salvatoreraccardi/OBJEX_LINK/boards/OBJEX_LINK-Rev1.7-C3_RISC-V/OBJEX Link v1.7-C3.jpg

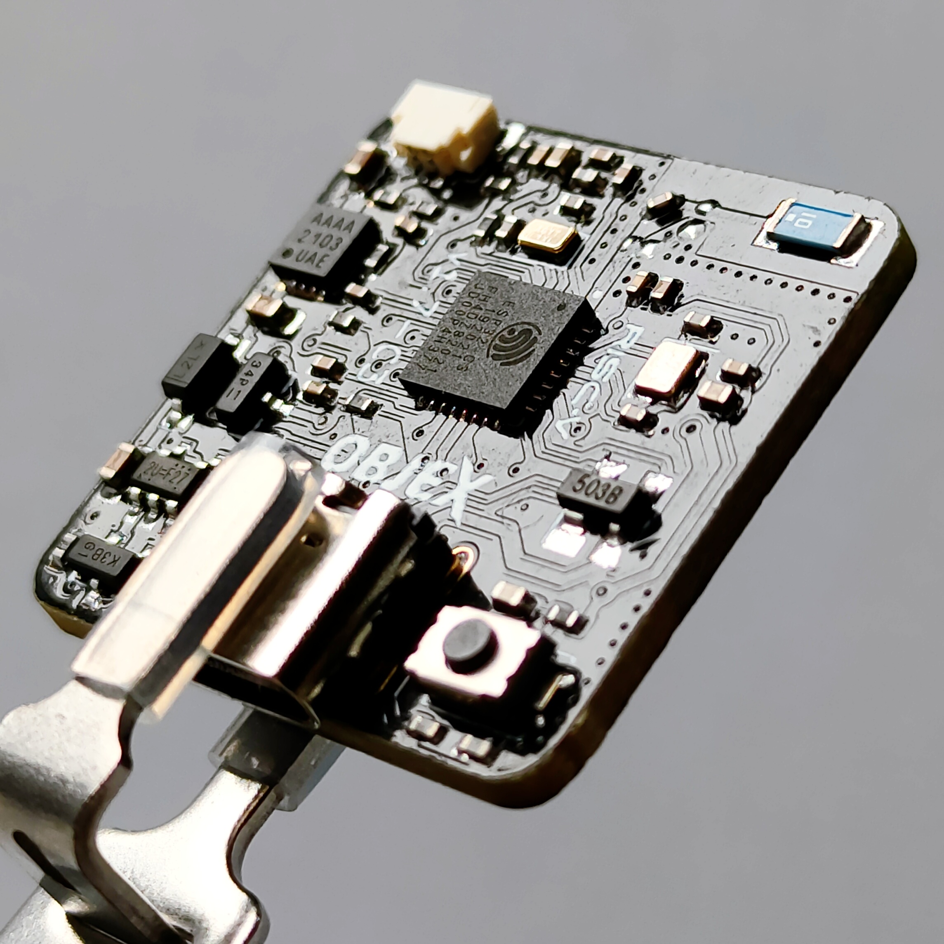
boards/OBJEX_LINK-Rev1.7-C3_RISC-V/OBJEX Link v1.7-C3.jpg
