salvatoreraccardi/OBJEX_LINK/dir/1-2.jpg

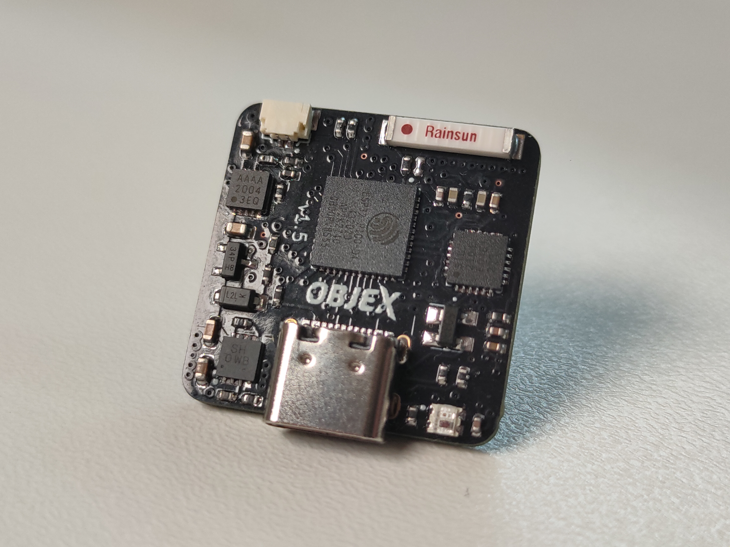
dir/1-2.jpg
