salvatoreraccardi/OBJEX_LINK/dir/1.jpg

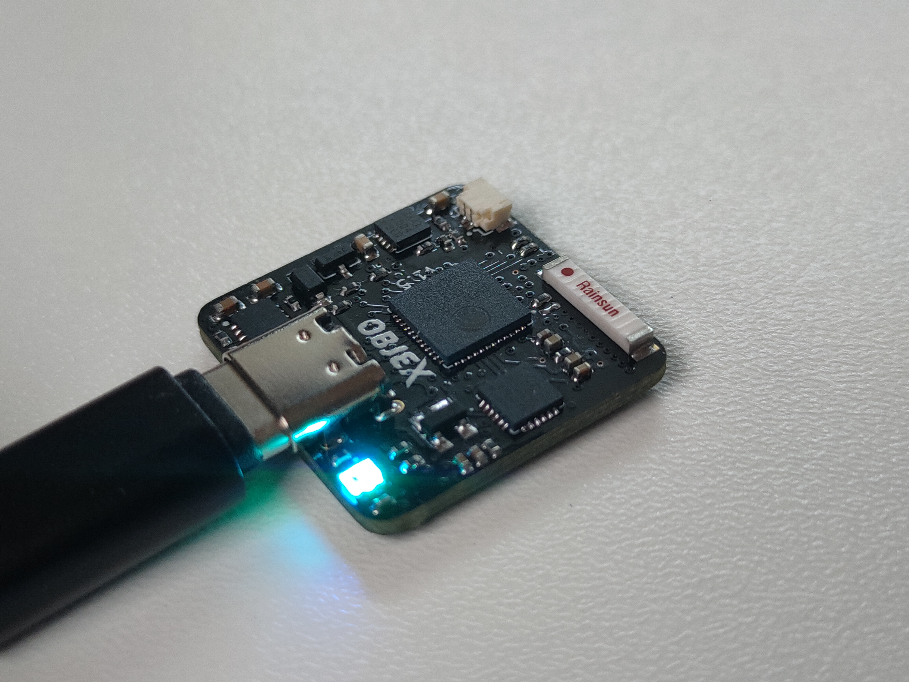
dir/1.jpg
