salvatoreraccardi/OBJEX_LINK/dir/2-1.png

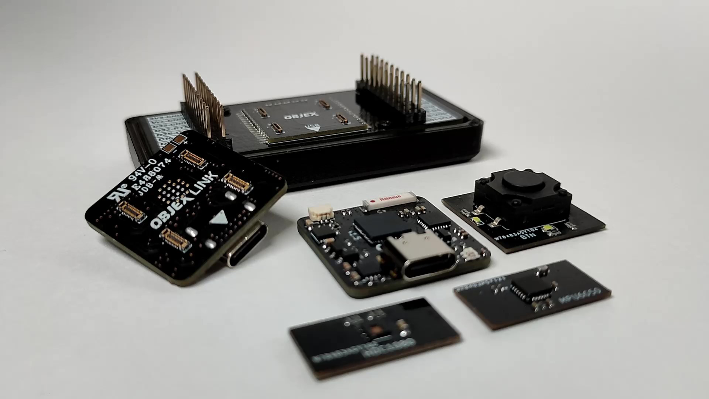
dir/2-1.png
