salvatoreraccardi/OBJEX_LINK/dir/2-3.jpg

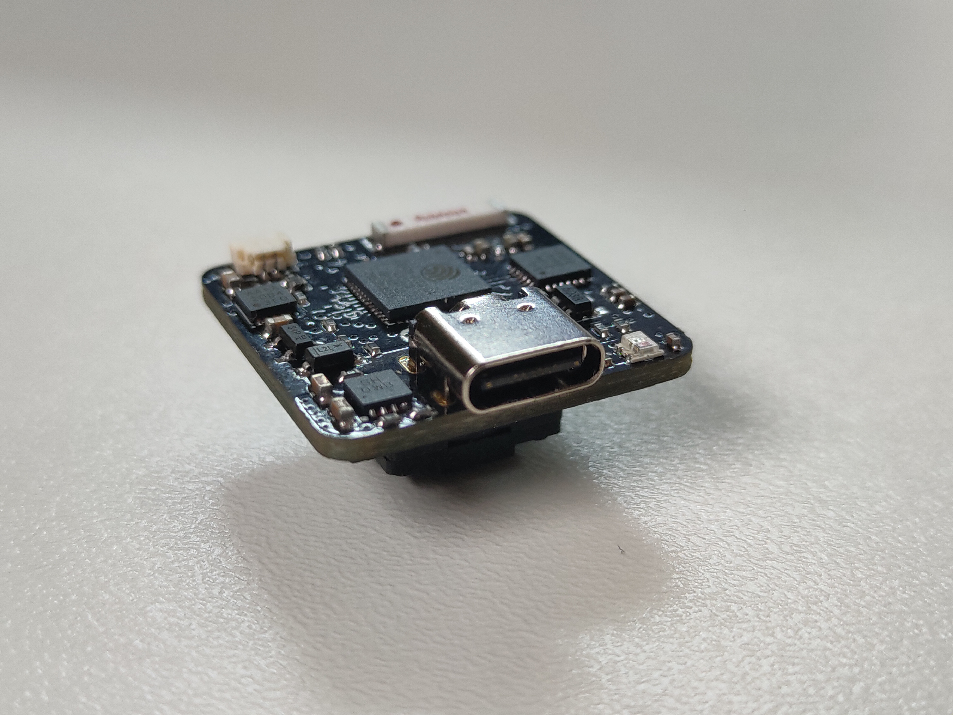
dir/2-3.jpg
