salvatoreraccardi/OBJEX_LINK/dir/2.jpg

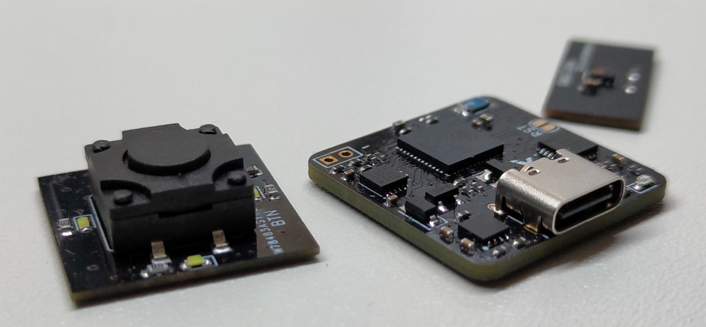
dir/2.jpg
