salvatoreraccardi/OBJEX_LINK/dir/3.jpg

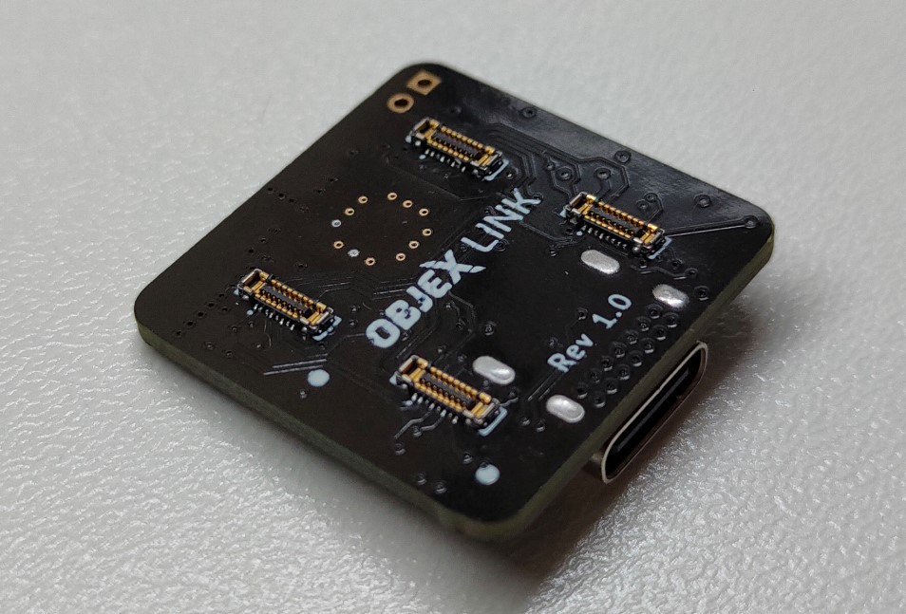
dir/3.jpg
