salvatoreraccardi/OBJEX_LINK/dir/3D_2.jpg

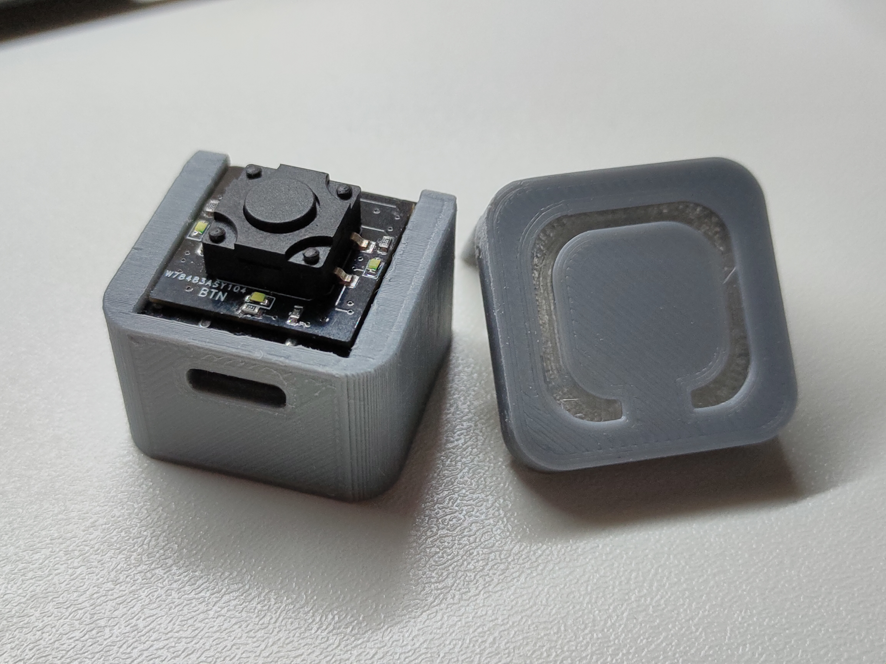
dir/3D_2.jpg
