salvatoreraccardi/OBJEX_LINK/dir/3D_3.jpg

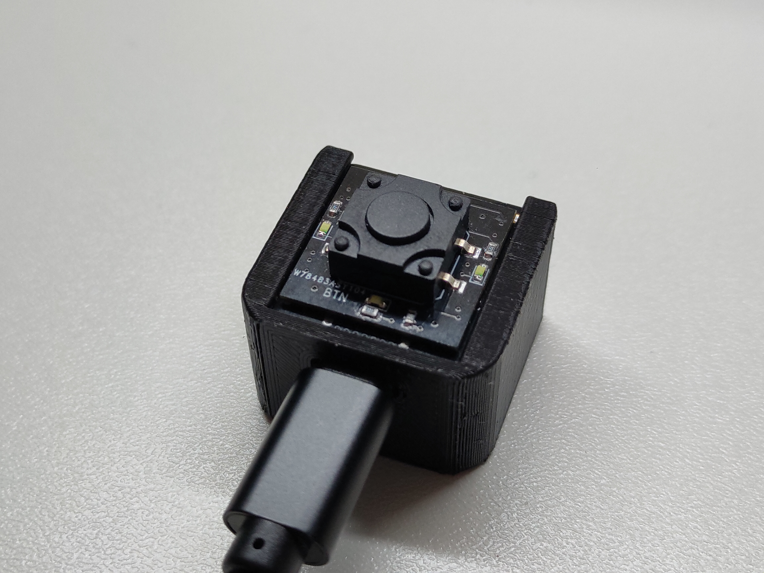
dir/3D_3.jpg
