salvatoreraccardi/OBJEX_LINK/dir/3D_4.jpg

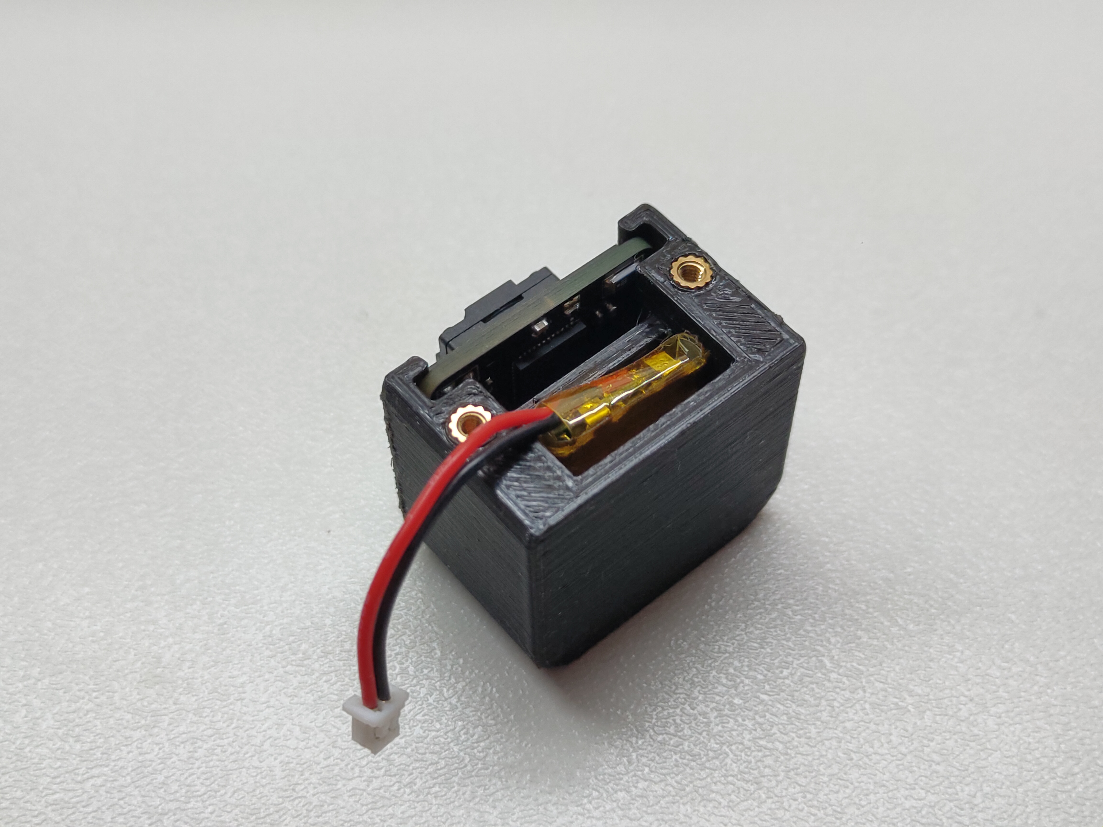
dir/3D_4.jpg
