salvatoreraccardi/OBJEX_LINK/dir/3D_5.jpg

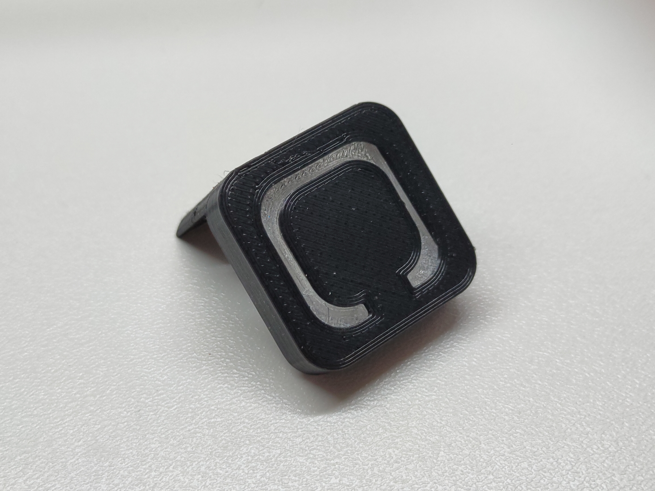
dir/3D_5.jpg
