salvatoreraccardi/OBJEX_LINK/dir/4.jpg

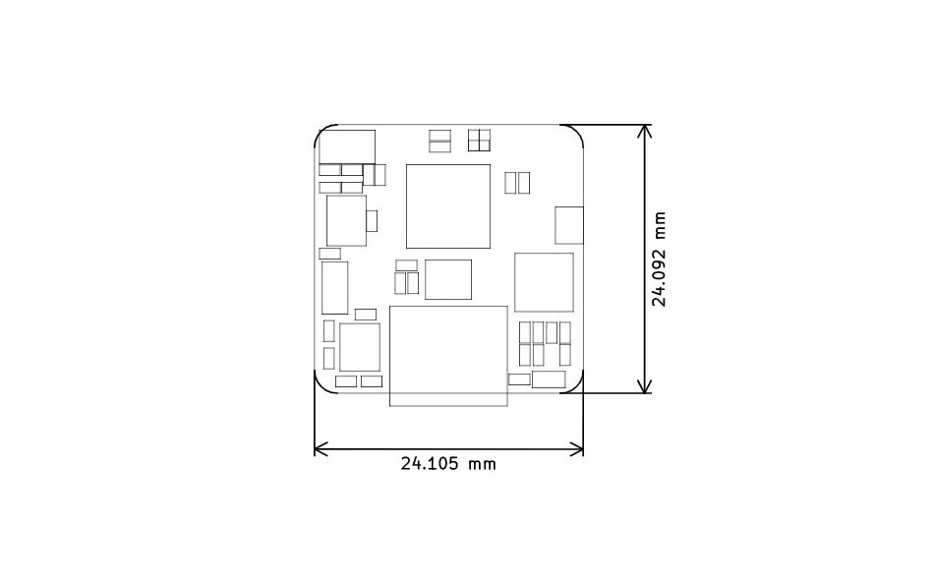
dir/4.jpg
