salvatoreraccardi/OBJEX_LINK/dir/5.jpg

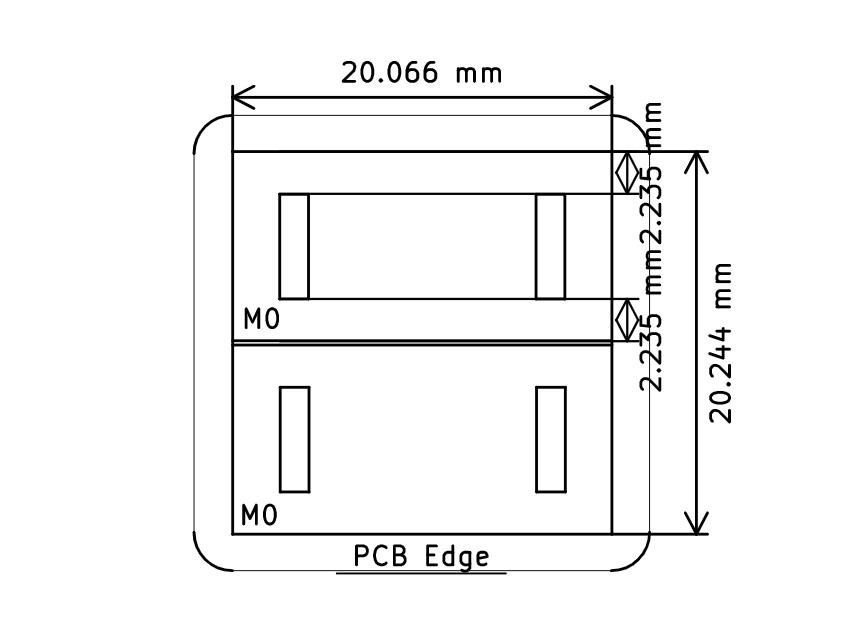
dir/5.jpg
