salvatoreraccardi/OBJEX_LINK/dir/blockdiagram/1.png

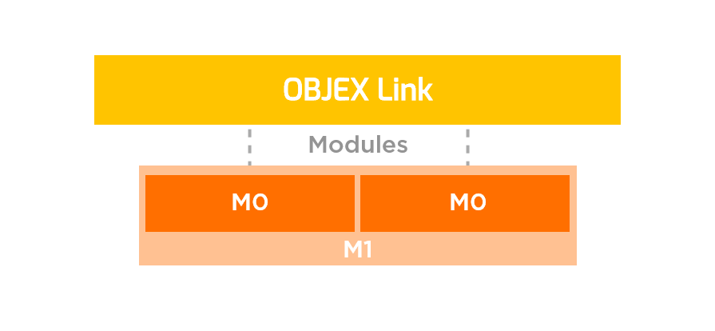
dir/blockdiagram/1.png
