salvatoreraccardi/OBJEX_LINK/dir/Blockdiagram_1.png

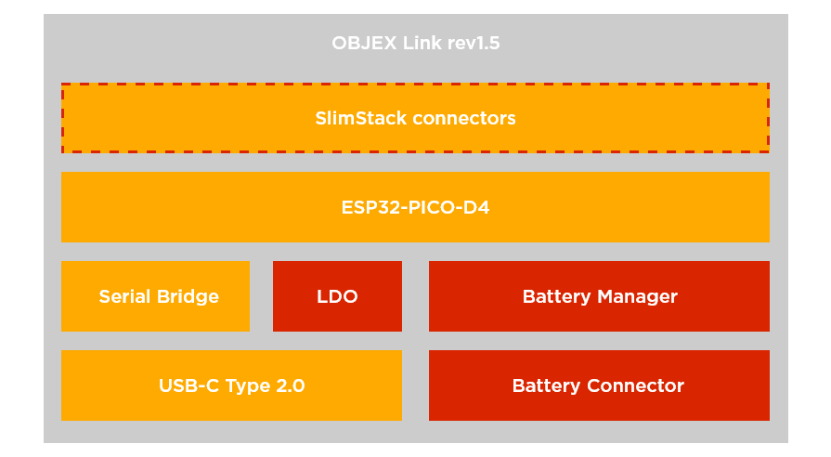
dir/Blockdiagram_1.png
