salvatoreraccardi/OBJEX_LINK/dir/Flex_1.png

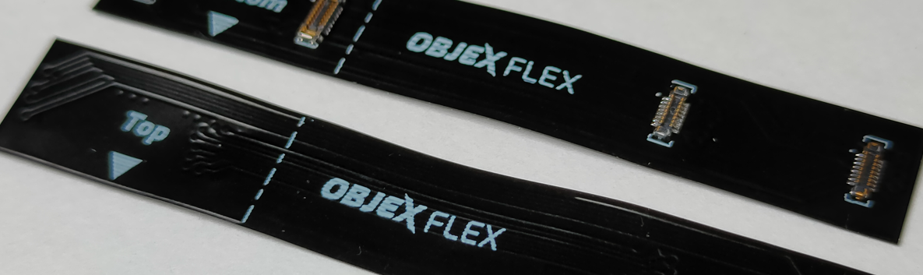
dir/Flex_1.png
