salvatoreraccardi/OBJEX_LINK/dir/Flex_2.png

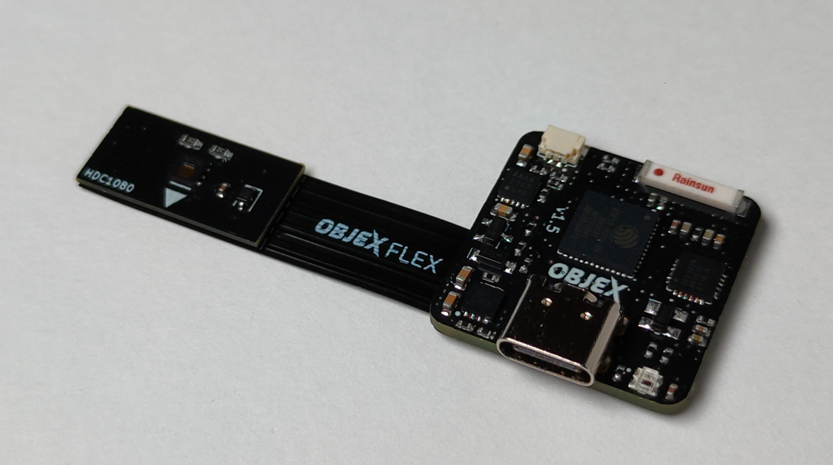
dir/Flex_2.png
