salvatoreraccardi/OBJEX_LINK/dir/Flex_3.png

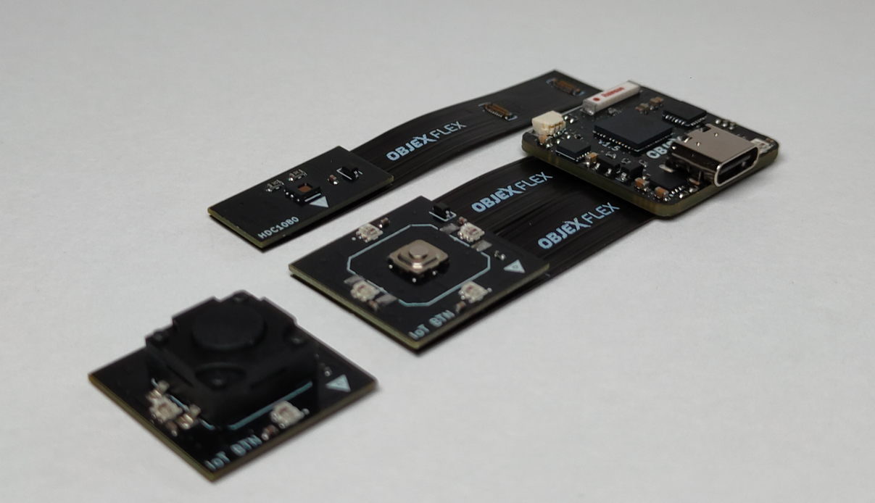
dir/Flex_3.png
