salvatoreraccardi/OBJEX_LINK/dir/Flex_4.png

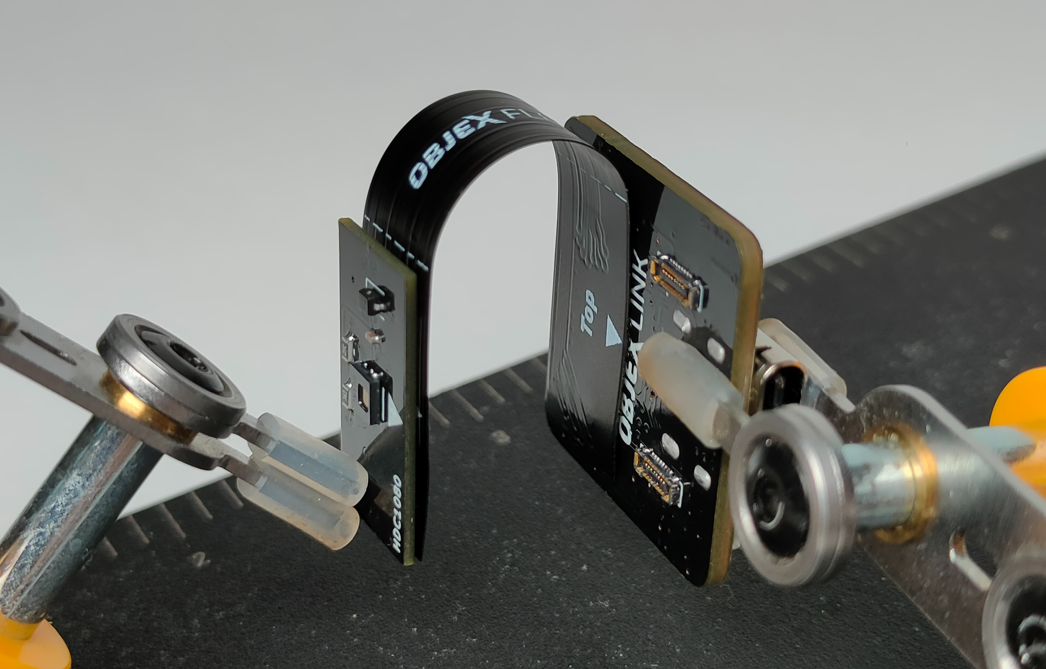
dir/Flex_4.png
