salvatoreraccardi/OBJEX_LINK/dir/Flex_5.png

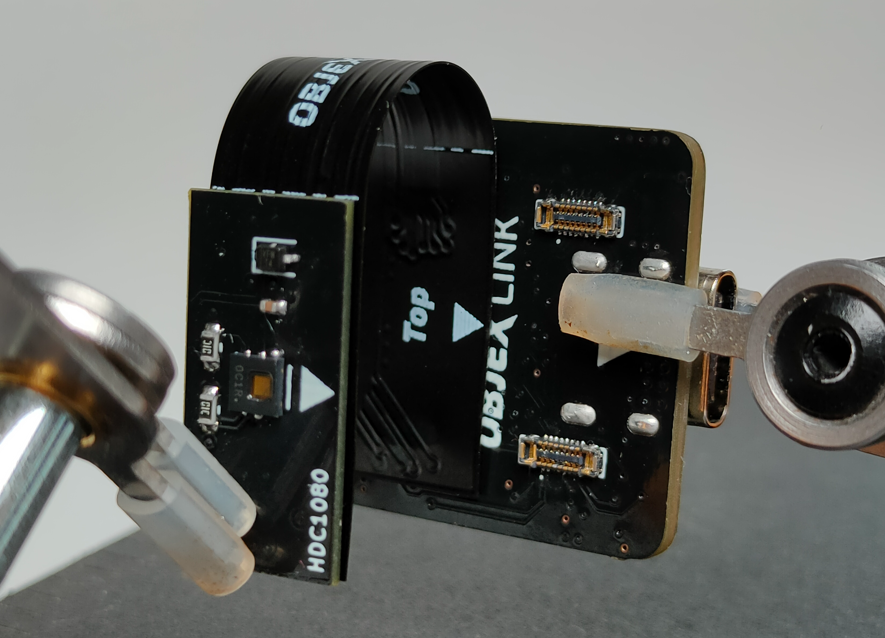
dir/Flex_5.png
