salvatoreraccardi/OBJEX_LINK/dir/Flex_7.jpg

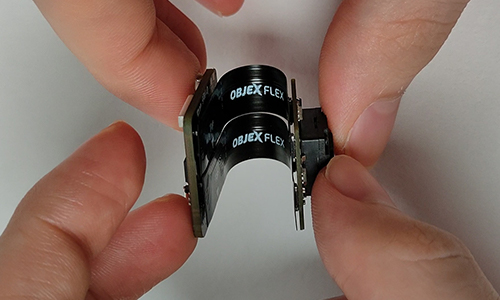
dir/Flex_7.jpg
