salvatoreraccardi/OBJEX_LINK/dir/graph-pwr_consumpition.png

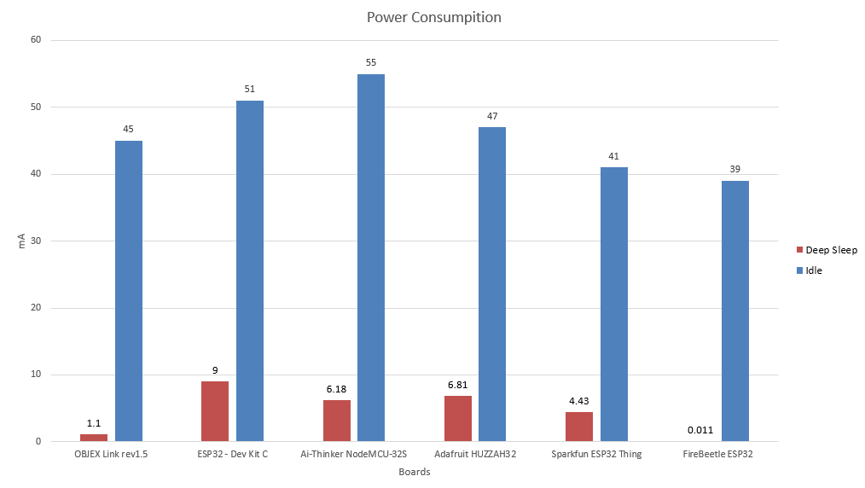
dir/graph-pwr_consumpition.png
