salvatoreraccardi/OBJEX_LINK/dir/IMG20210604104828.jpg

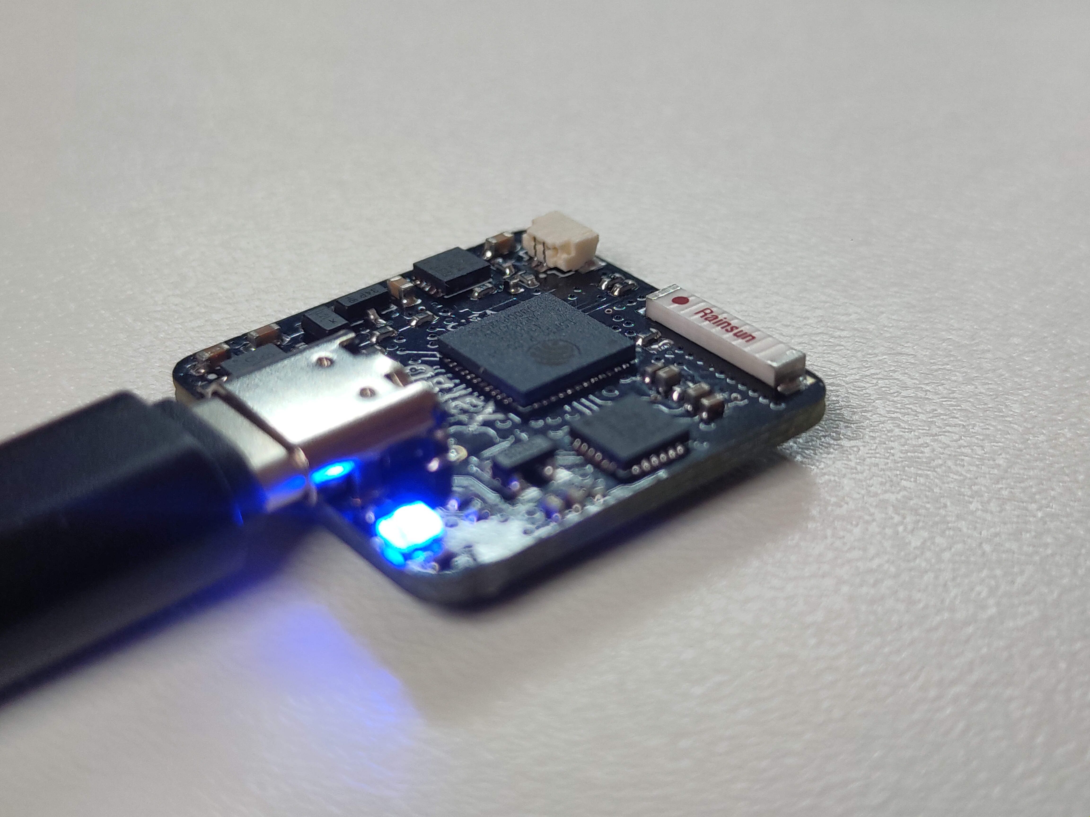
dir/IMG20210604104828.jpg
