salvatoreraccardi/OBJEX_LINK/dir/IMG20210604105308.jpg

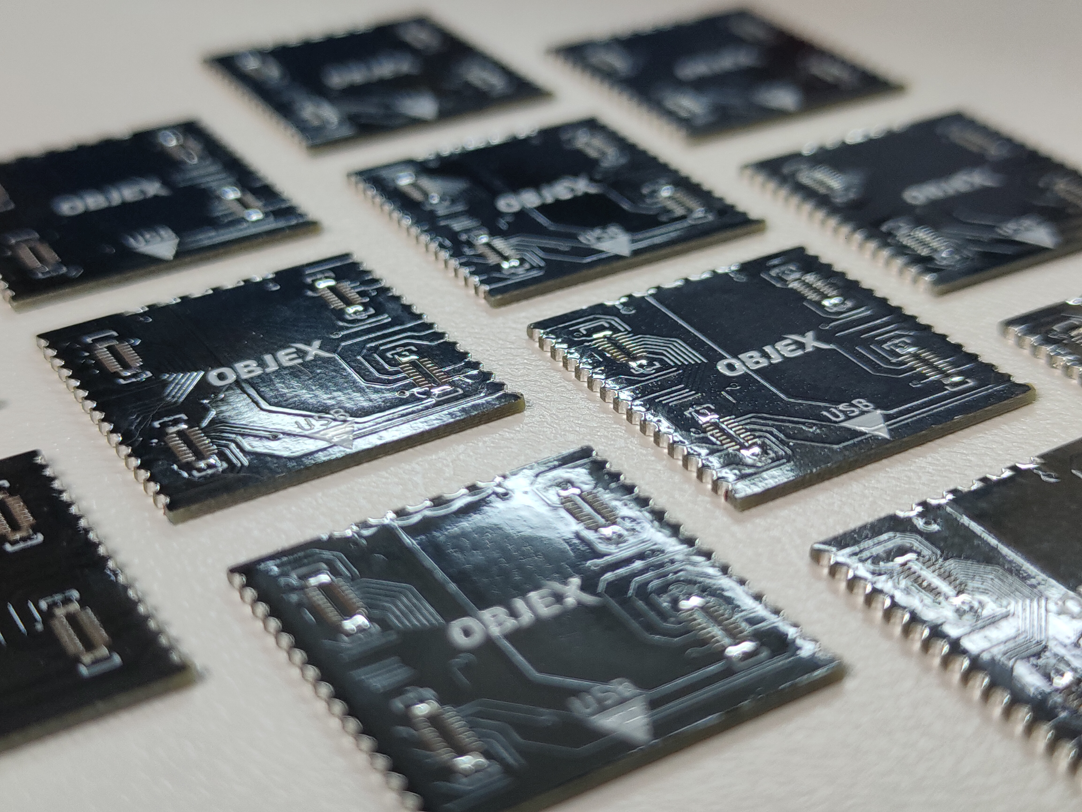
dir/IMG20210604105308.jpg
