salvatoreraccardi/OBJEX_LINK/dir/IMG20210604105436.jpg

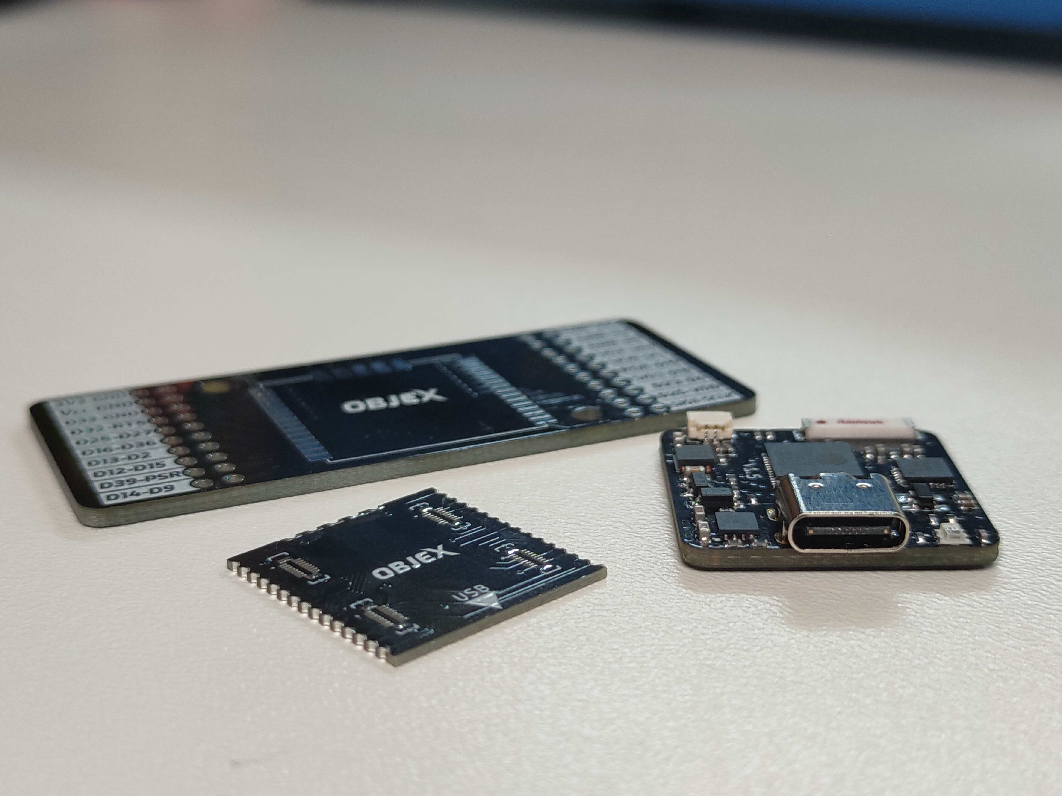
dir/IMG20210604105436.jpg
