salvatoreraccardi/OBJEX_LINK/dir/iotbuttonTypeA.png

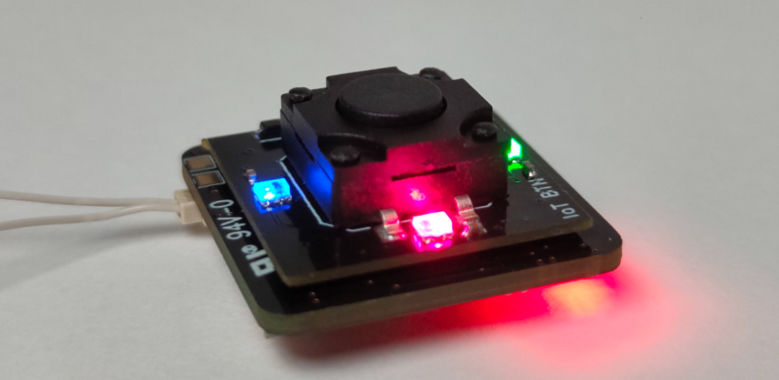
dir/iotbuttonTypeA.png
