salvatoreraccardi/OBJEX_LINK/dir/modules/HDC1080_1.5.png

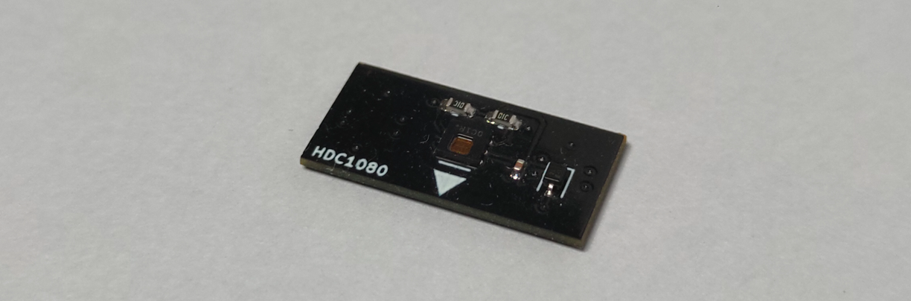
dir/modules/HDC1080_1.5.png
