salvatoreraccardi/OBJEX_LINK/dir/modules/IoT_btn_rgb-1.png

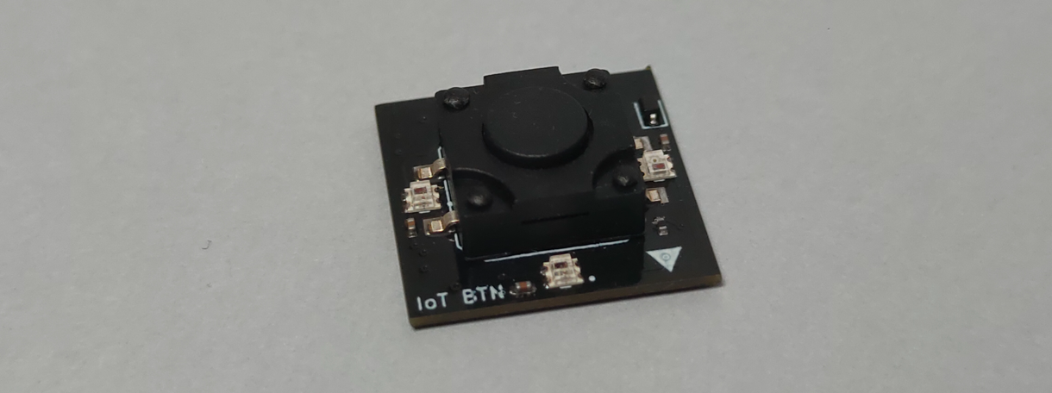
dir/modules/IoT_btn_rgb-1.png
