salvatoreraccardi/OBJEX_LINK/dir/modules/IoT_btn_rgb-2.png

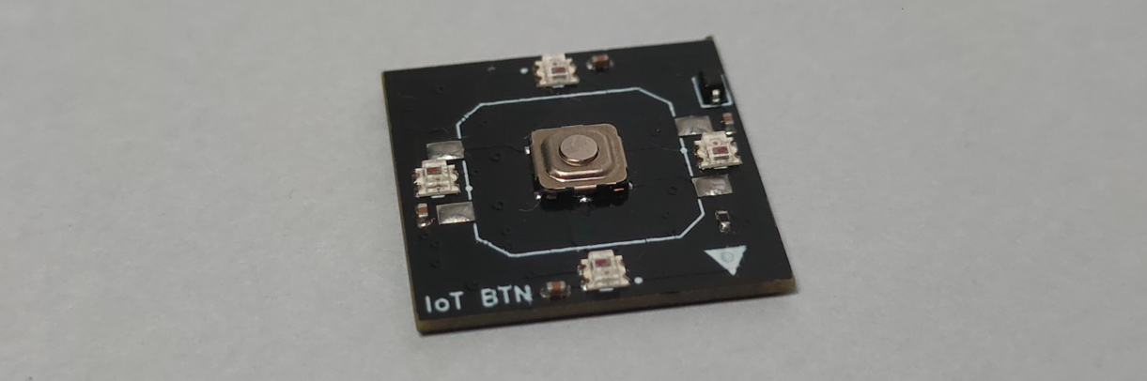
dir/modules/IoT_btn_rgb-2.png
