salvatoreraccardi/OBJEX_LINK/dir/modules/MPU6050_1.0.png

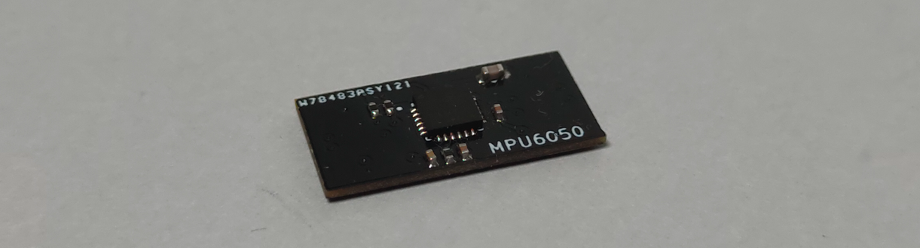
dir/modules/MPU6050_1.0.png
