salvatoreraccardi/OBJEX_LINK/dir/modules/ProtoBoard.png

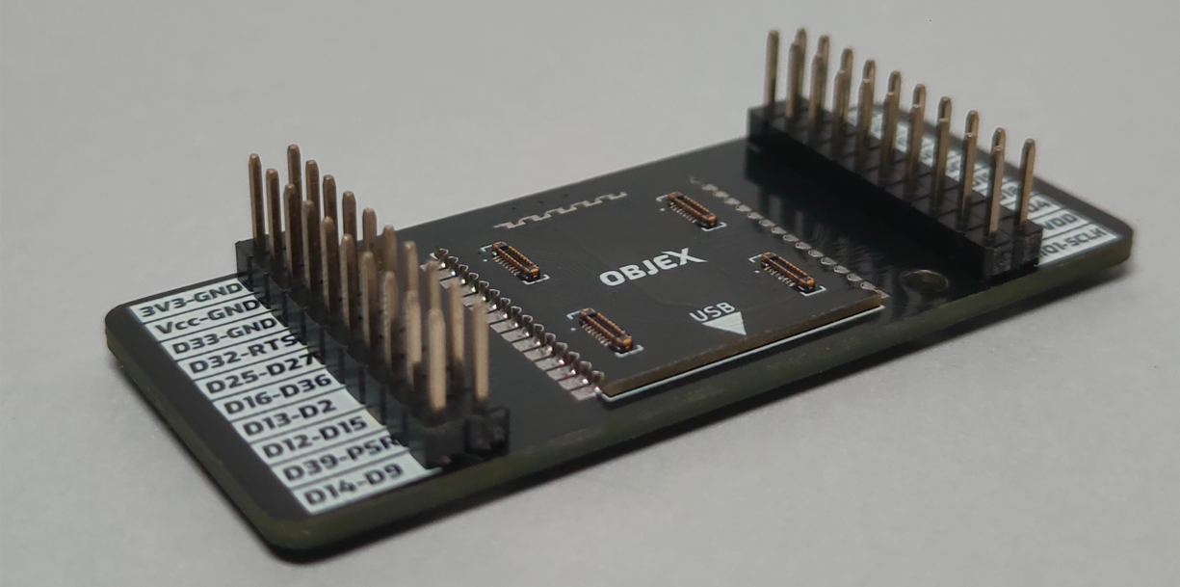
dir/modules/ProtoBoard.png
