salvatoreraccardi/OBJEX_LINK/dir/objexlink&modules.png

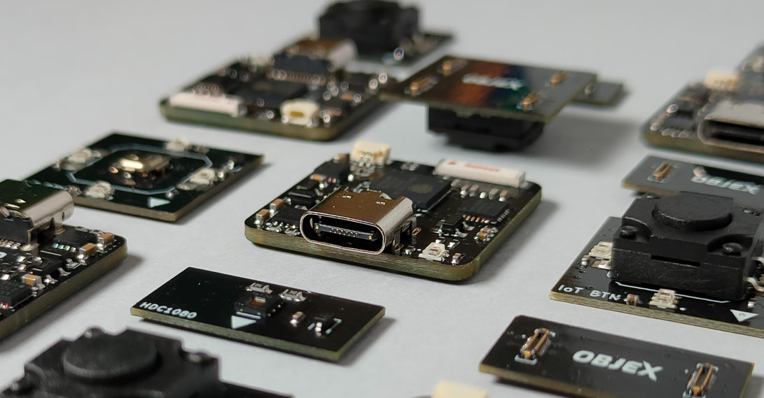
dir/objexlink&modules.png
