salvatoreraccardi/OBJEX_LINK/dir/Protoboard_1.png

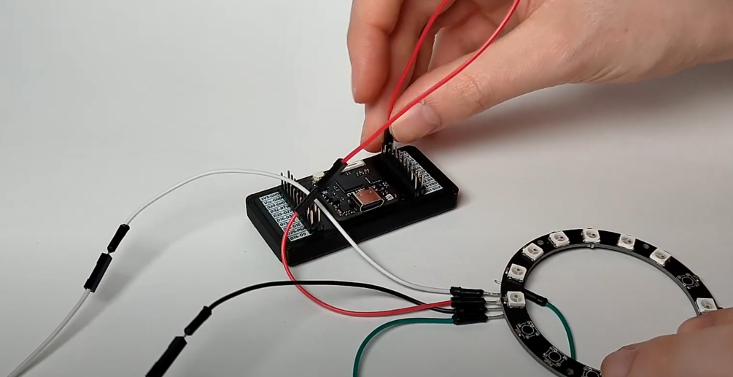
dir/Protoboard_1.png
