salvatoreraccardi/OBJEX_LINK/dir/QuickStart/1.png

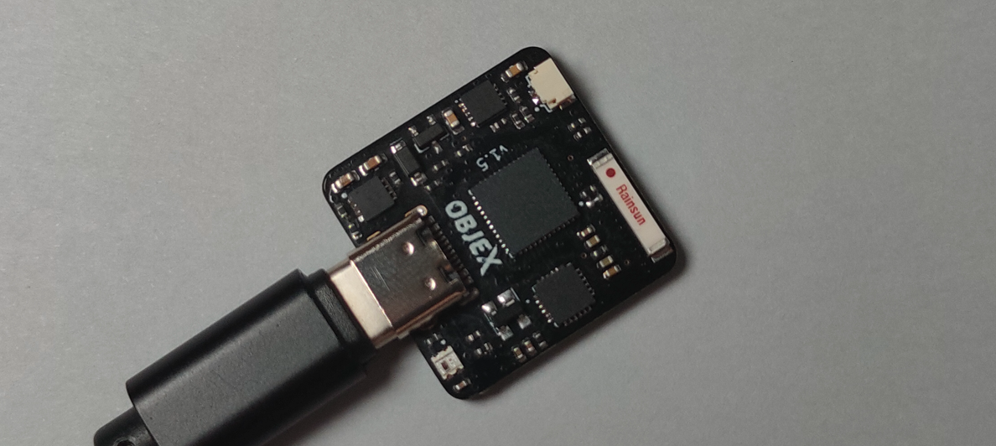
dir/QuickStart/1.png
