salvatoreraccardi/OBJEX_LINK/dir/QuickStart/2.png

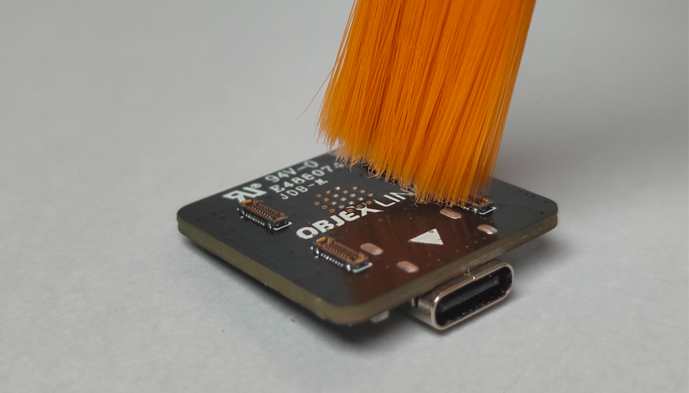
dir/QuickStart/2.png
