salvatoreraccardi/OBJEX_LINK/dir/QuickStart/3.png

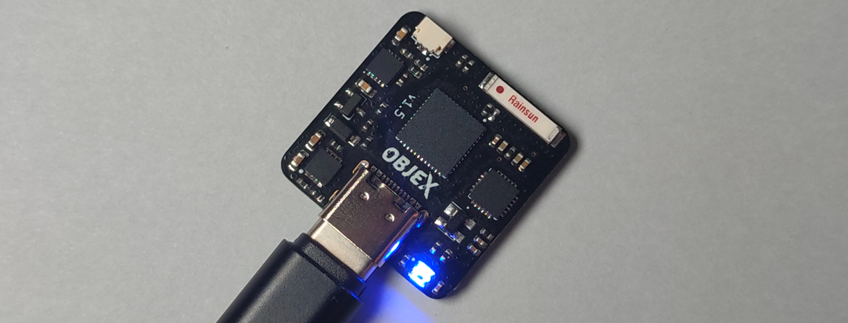
dir/QuickStart/3.png
