salvatoreraccardi/OBJEX_LINK/dir/QuickStart/4.png

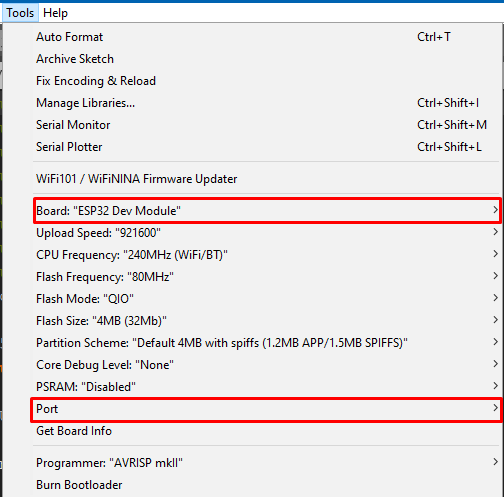
dir/QuickStart/4.png
