salvatoreraccardi/OBJEX_LINK/dir/QuickStart/5.png

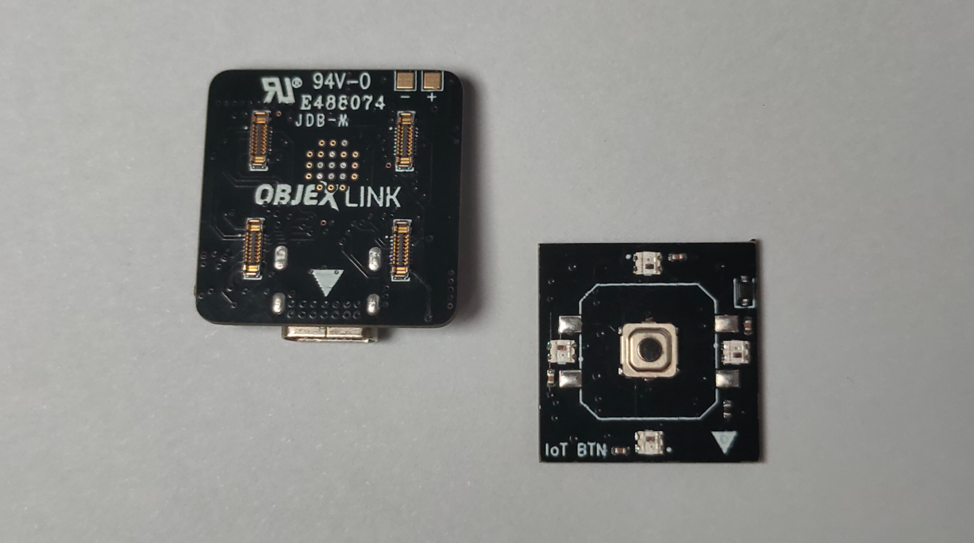
dir/QuickStart/5.png
