salvatoreraccardi/OBJEX_LINK/dir/QuickStart/6.png

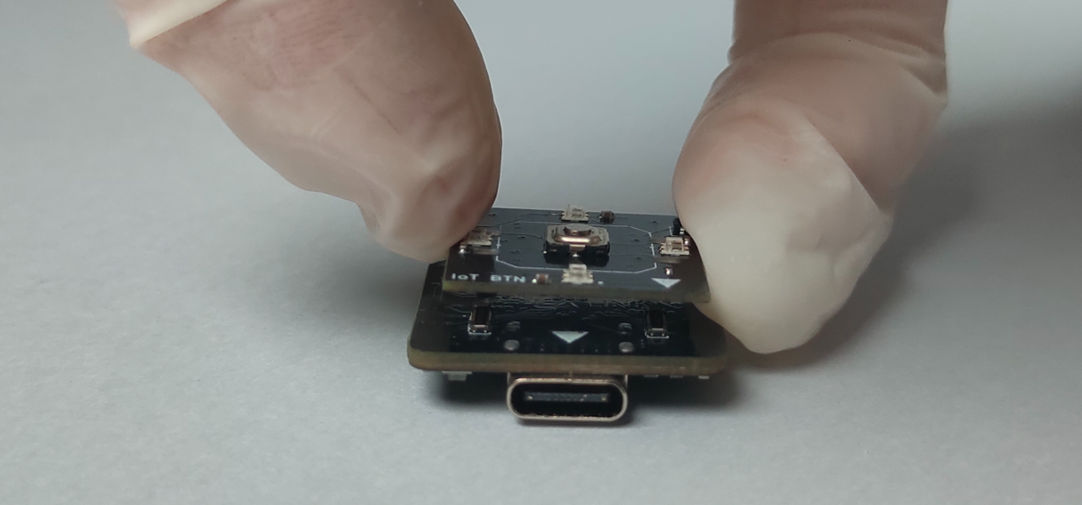
dir/QuickStart/6.png
