salvatoreraccardi/OBJEX_LINK/dir/QuickStart/7.png

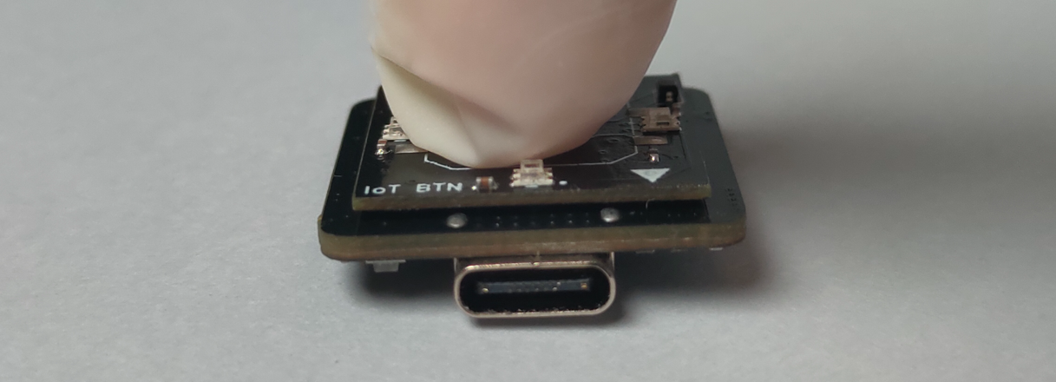
dir/QuickStart/7.png
