salvatoreraccardi/OBJEX_LINK/dir/QuickStart/8.png

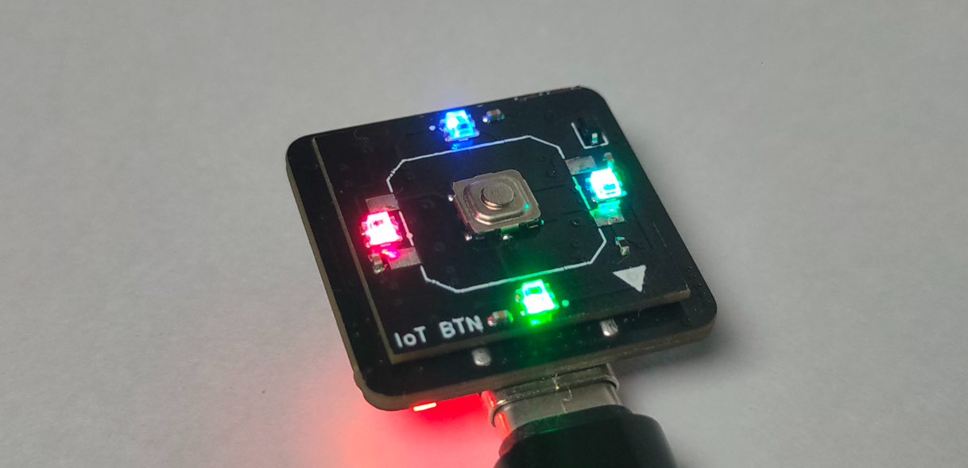
dir/QuickStart/8.png
