salvatoreraccardi/OBJEX_LINK/dir/QuickStart/9.png

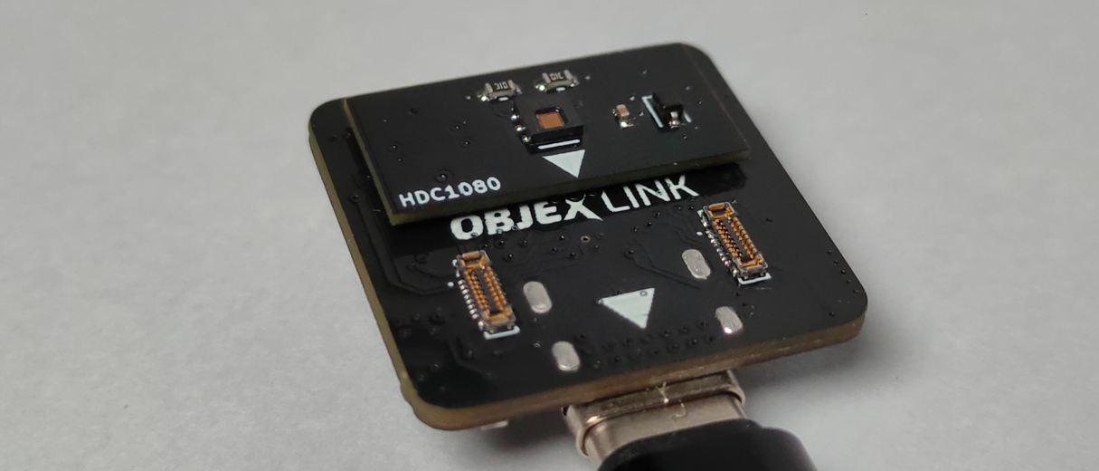
dir/QuickStart/9.png
