salvatoreraccardi/OBJEX_LINK/dir/QuickStart/10.png

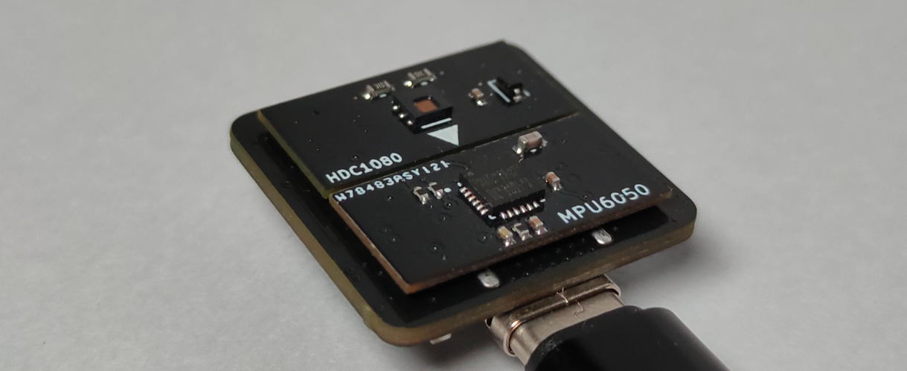
dir/QuickStart/10.png
