salvatoreraccardi/OBJEX_LINK/dir/QuickStart/12.png

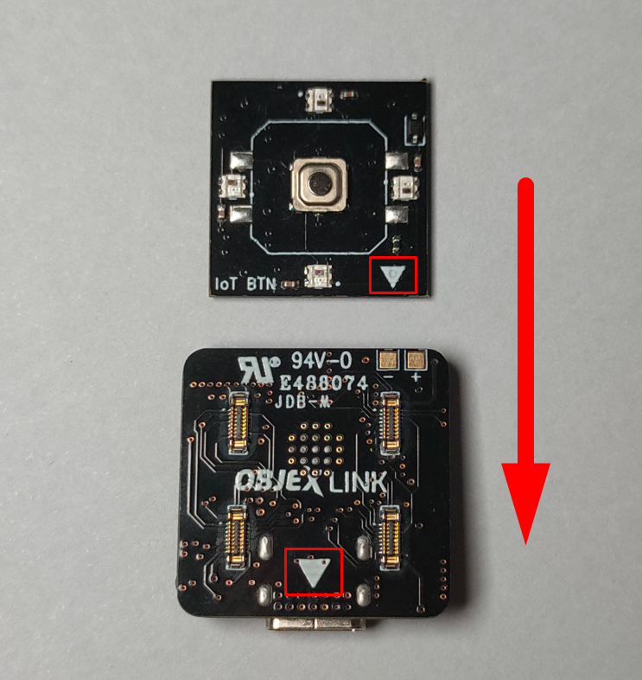
dir/QuickStart/12.png
