salvatoreraccardi/OBJEX_LINK/dir/rprog.png

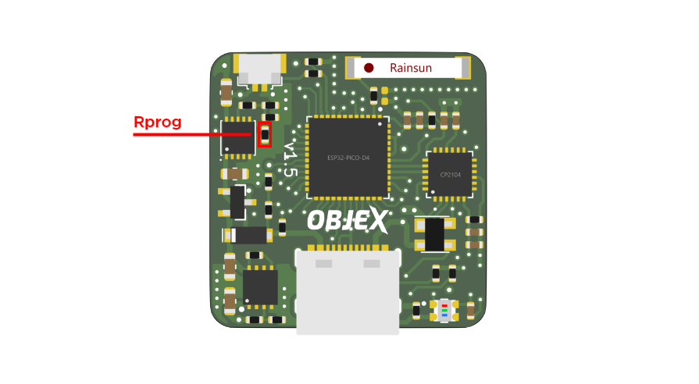
dir/rprog.png
