salvatoreraccardi/OBJEX_LINK/dir/socket_1.png

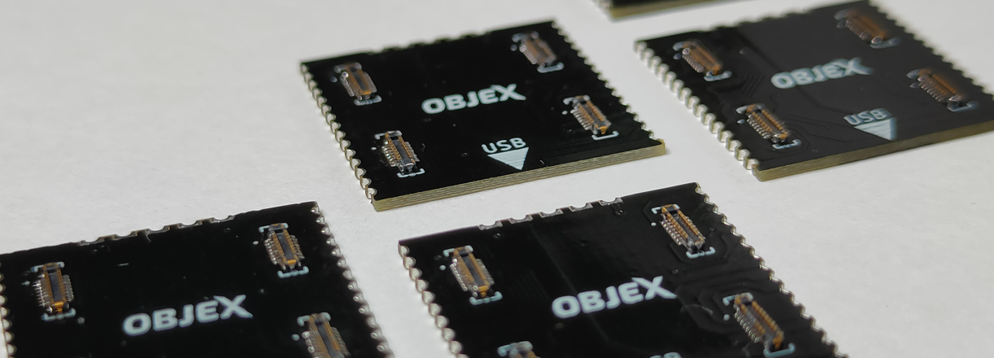
dir/socket_1.png
