salvatoreraccardi/OBJEX_LINK/dir/TSG_buttonB.png

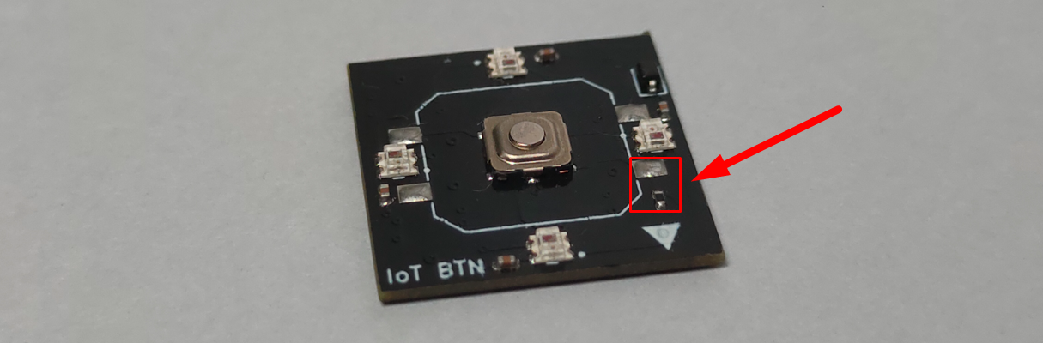
dir/TSG_buttonB.png
