salvatoreraccardi/OBJEX_LINK/dir/VID20210618144237_Moment.jpg

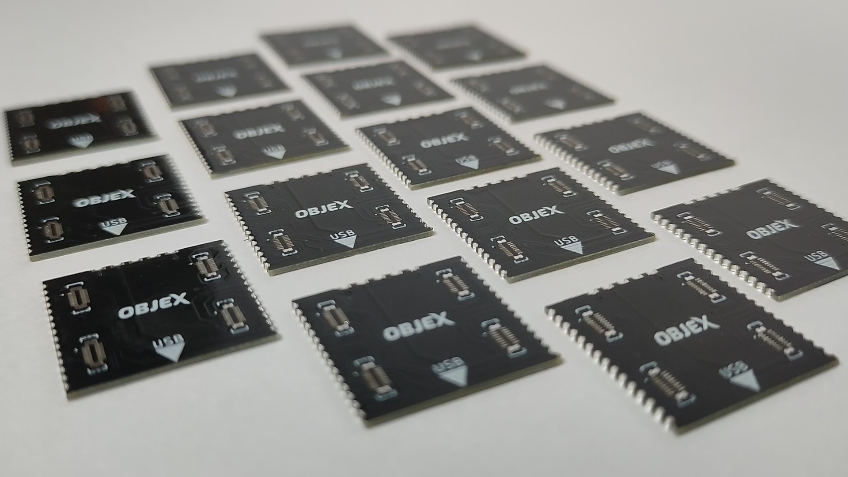
dir/VID20210618144237_Moment.jpg
