salvatoreraccardi/OBJEX_LINK/3d/IoT_Button/beta-1.0/Master.stl

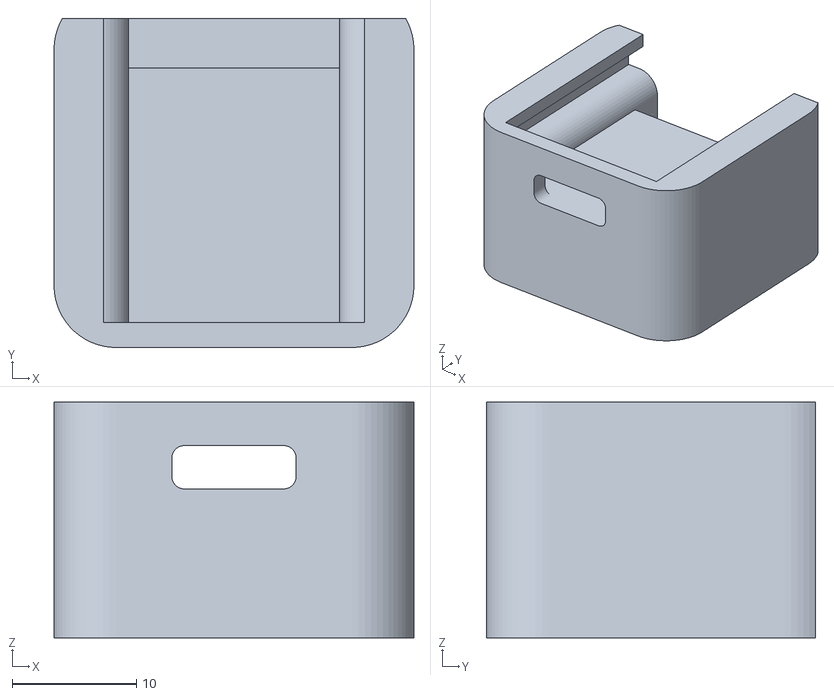
[picture p74: CAD file, 2021-04-03, an earlier design]
3d/IoT_Button/beta-1.0/Master.stl
29.0 x 26.5 x 19.0
