salvatoreraccardi/OBJEX_LINK/boards/OBJEX_LINK-Rev1.5/OBJEX_LINK-Rev1.5.pdf

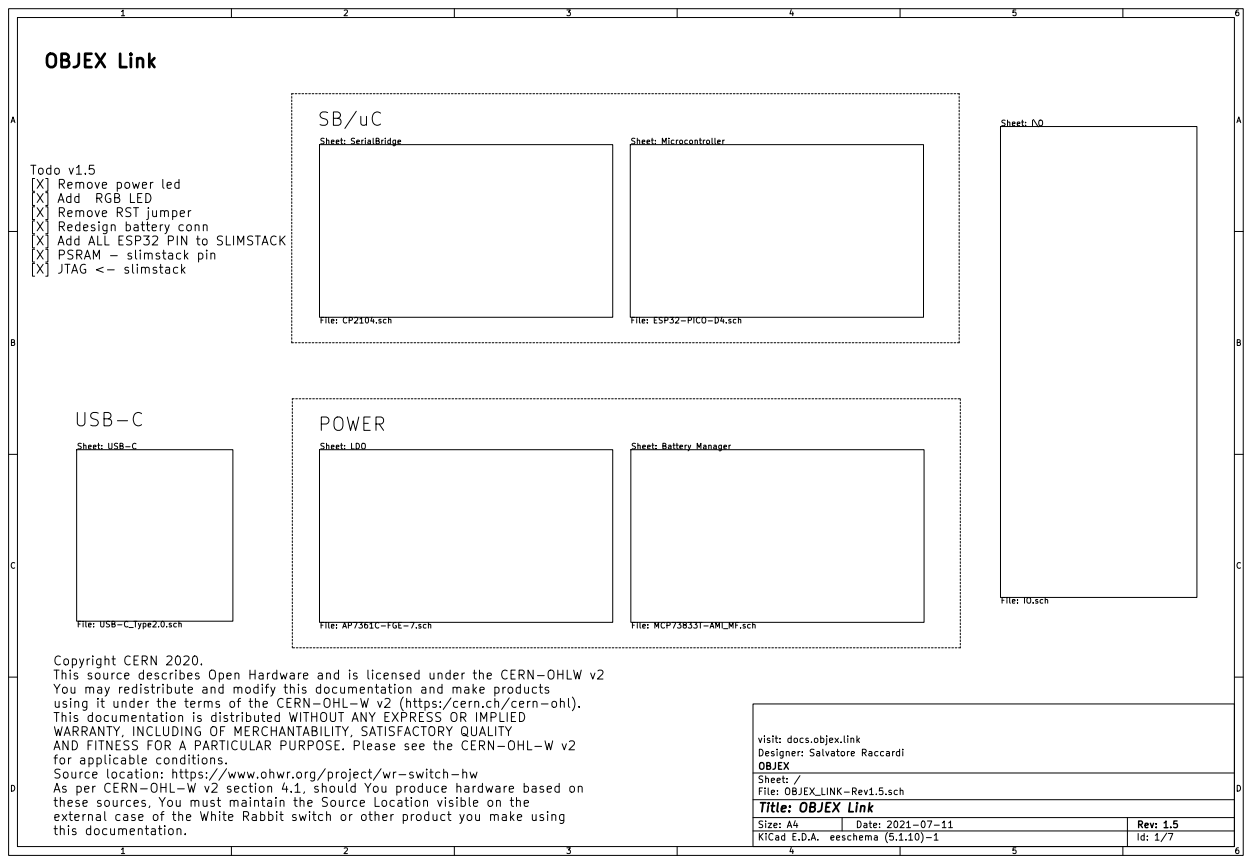
[picture p99: page 1]

Sheet: SerialBridge File: CP2104.sch Sheet: LDO

Sheet: Microcontroller File: ESP32-PICO-D4.sch SB/uC

Todo v1.5
[X] Remove power led
[X] Remove RST jumper
[X] Redesign battery conn
[X] Add ALL ESP32 PIN to SLIMSTACK
[X] PSRAM - slimstack pin
[X] JTAG <- slimstack

File: IO.sch Sheet: USB-C

Copyright CERN 2020.
This source describes Open Hardware and is licensed under the CERN-OHLW v2
You may redistribute and modify this documentation and make products
using it under the terms of the CERN-OHL-W v2 (https:/cern.ch/cern-ohl).
This documentation is distributed WITHOUT ANY EXPRESS OR IMPLIED
WARRANTY, INCLUDING OF MERCHANTABILITY, SATISFACTORY QUALITY
AND FITNESS FOR A PARTICULAR PURPOSE. Please see the CERN-OHL-W v2
for applicable conditions.
Source location: https://www.ohwr.org/project/wr-switch-hw
As per CERN-OHL-W v2 section 4.1, should You produce hardware based on
these sources, You must maintain the Source Location visible on the
external case of the White Rabbit switch or other product you make using
this documentation.

visit: docs.objex.link
File: OBJEX_LINK-Rev1.5.sch Sheet: / OBJEX Designer: Salvatore Raccardi

Id: 1/7 Title: OBJEX Link

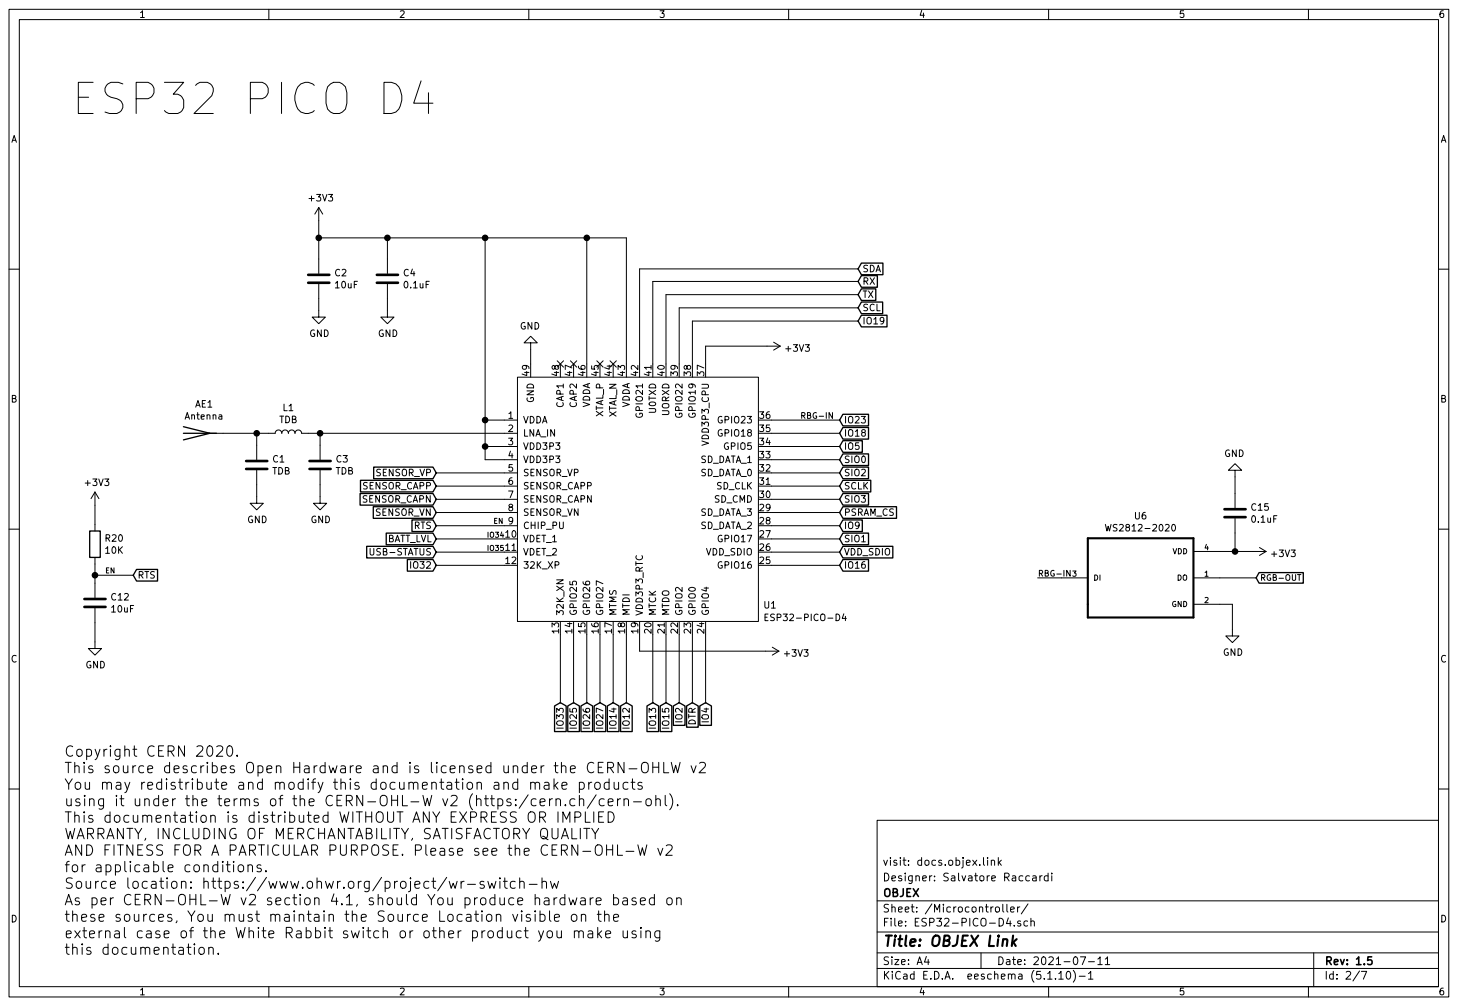
[picture p100: page 2]
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

visit: docs.objex.link
File: ESP32-PICO-D4.sch Sheet: /Microcontroller/ OBJEX Designer: Salvatore Raccardi

Id: 2/7 Title: OBJEX Link

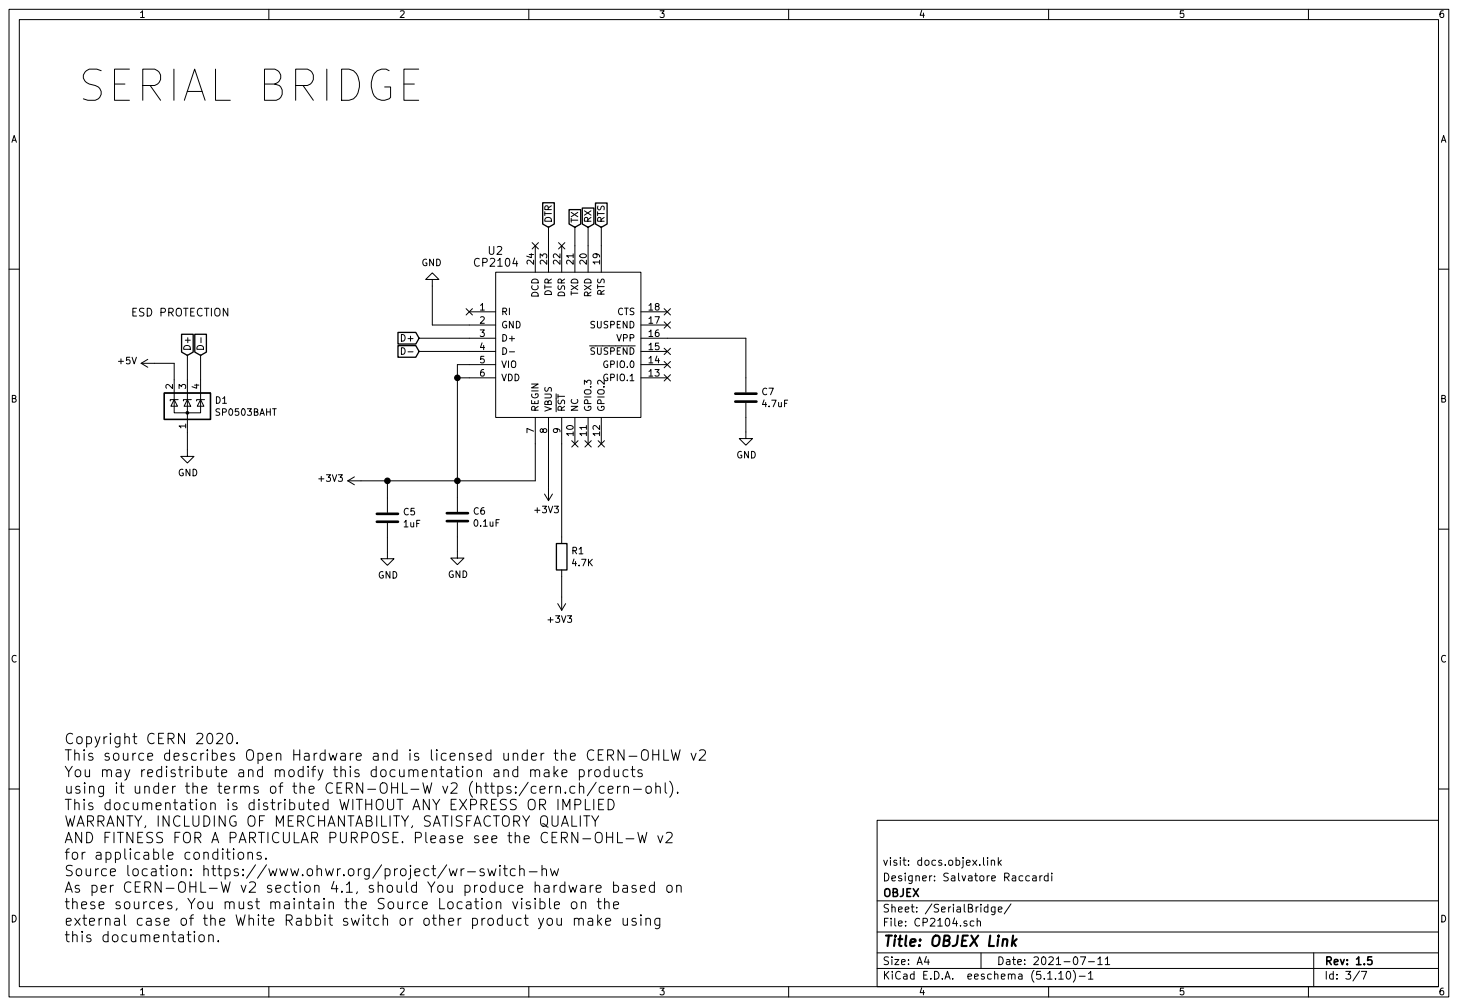
[picture p101: page 3]

SERIAL BRIDGE
ESD PROTECTION Copyright CERN 2020.

9 NC 10 RXD 20 GPIO.3 11 TXD 21 GPIO.2 12 DSR 22 GPIO.1 13 DTR 23 GPIO.0 14 DCD 24 SUSPEND 15 VPP 16 SUSPEND 17 CTS 18 RTS 19U2 CP2104 GND
4.7uF GND

visit: docs.objex.link GND

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

File: CP2104.sch Sheet: /SerialBridge/ OBJEX Designer: Salvatore Raccardi

Id: 3/7 Title: OBJEX Link

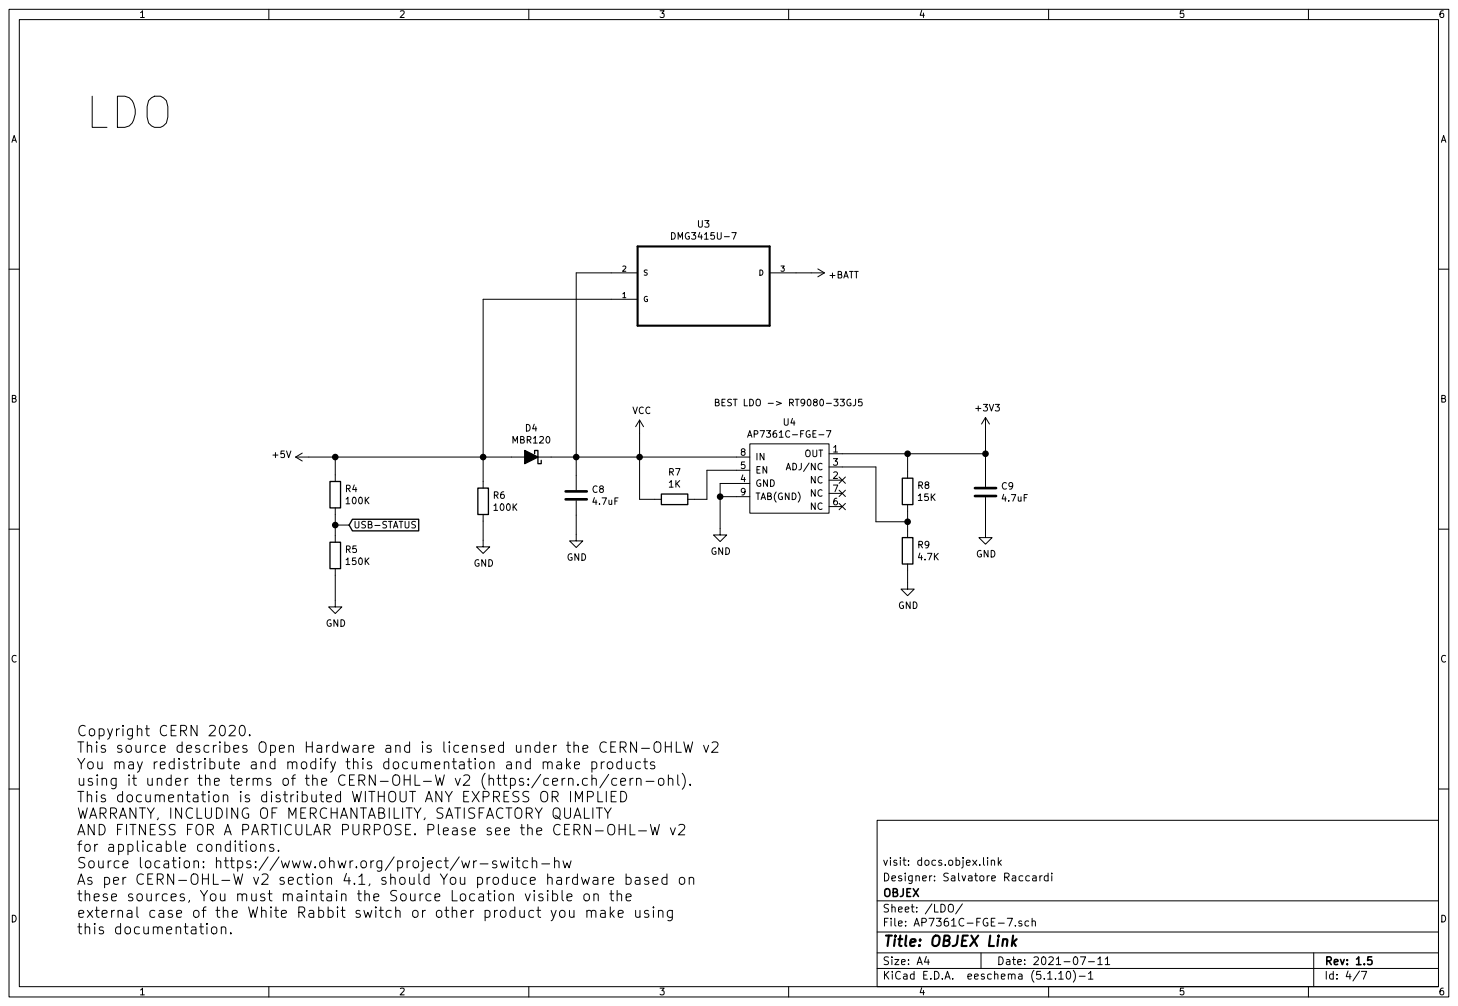
[picture p102: page 4]

BEST LDO -> RT9080-33GJ5 Copyright CERN 2020.

visit: docs.objex.link R7

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

File: AP7361C-FGE-7.sch Sheet: /LDO/ OBJEX Designer: Salvatore Raccardi

Id: 4/7 Title: OBJEX Link

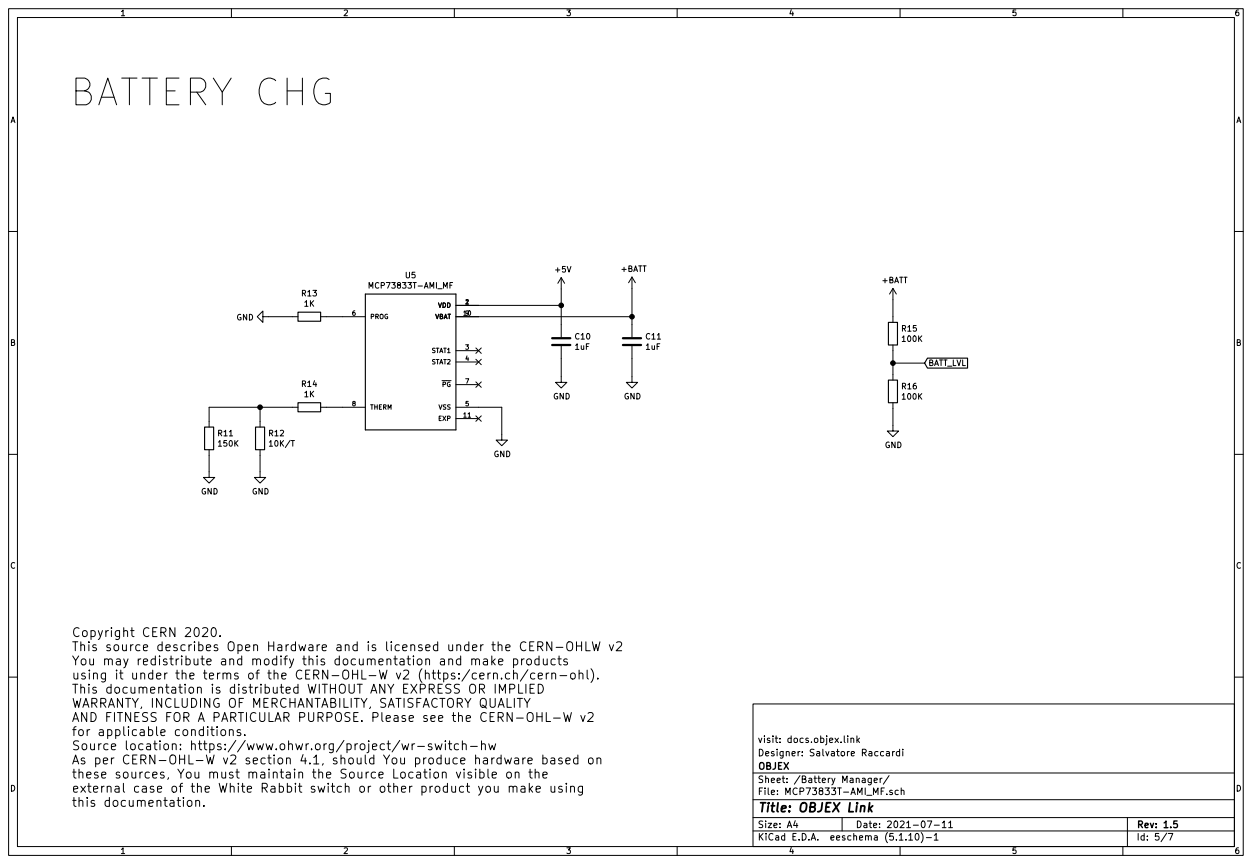
[picture p103: page 5]
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

visit: docs.objex.link
Sheet: /Battery Manager/ OBJEX Designer: Salvatore Raccardi

File: MCP73833T-AMI_MF.sch
Id: 5/7 Title: OBJEX Link


1M GND A1 | VBUS | B8 SHIELD S1

A4 CC1 A5 D+ A6 D-A7 SBU1 A8 CC2 B5 D+ B6 D-B7 SBU2

visit: docs.objex.link R17

File: USB-C_Type2.0.sch Sheet: /USB-C/ OBJEX Designer: Salvatore Raccardi

Id: 6/7 Title: OBJEX Link

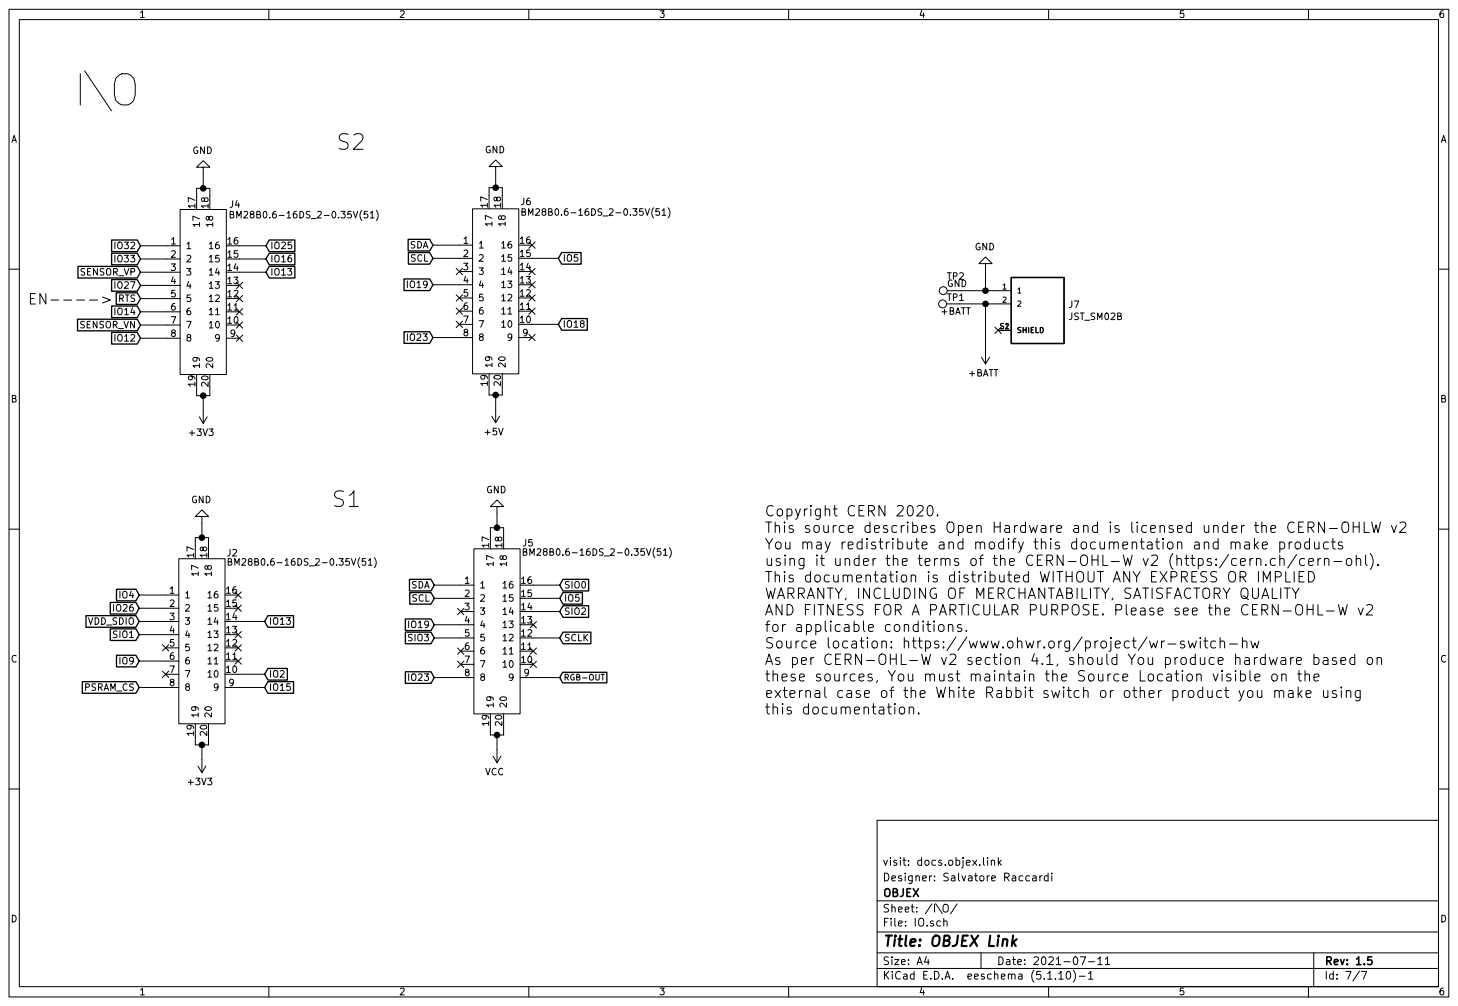
[picture p104: page 7]
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

visit: docs.objex.link
File: IO.sch Sheet: /I\O/ OBJEX Designer: Salvatore Raccardi

Id: 7/7 Title: OBJEX Link
