salvatoreraccardi/OBJEX_LINK/boards/OBJEX_LINK-Rev1.6-C3_RISC-V/OBJEX_LINK-Rev1.6_RISCV.pdf

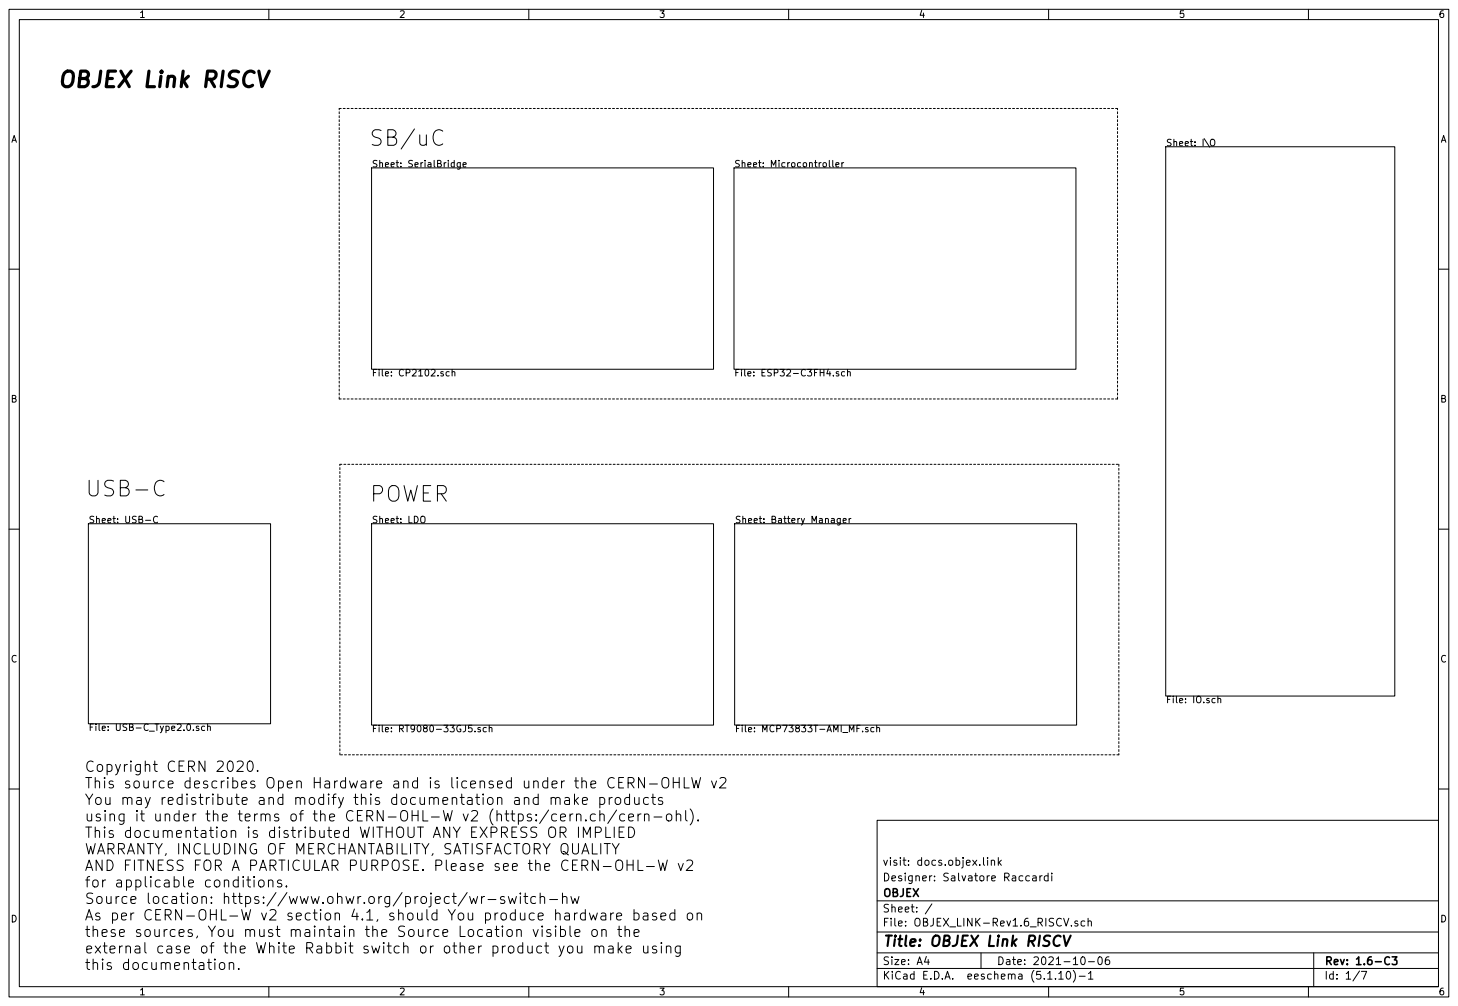
[picture p111: page 1]

Sheet: Battery Manager File: MCP73833T-AMI_MF.sch Sheet: USB-C

Copyright CERN 2020.
This source describes Open Hardware and is licensed under the CERN-OHLW v2
You may redistribute and modify this documentation and make products
using it under the terms of the CERN-OHL-W v2 (https:/cern.ch/cern-ohl).
This documentation is distributed WITHOUT ANY EXPRESS OR IMPLIED
WARRANTY, INCLUDING OF MERCHANTABILITY, SATISFACTORY QUALITY
AND FITNESS FOR A PARTICULAR PURPOSE. Please see the CERN-OHL-W v2
for applicable conditions.
Source location: https://www.ohwr.org/project/wr-switch-hw
As per CERN-OHL-W v2 section 4.1, should You produce hardware based on
these sources, You must maintain the Source Location visible on the
external case of the White Rabbit switch or other product you make using
this documentation.

visit: docs.objex.link
File: OBJEX_LINK-Rev1.6_RISCV.sch Sheet: / OBJEX Designer: Salvatore Raccardi

Id: 1/7 Title: OBJEX Link RISCV

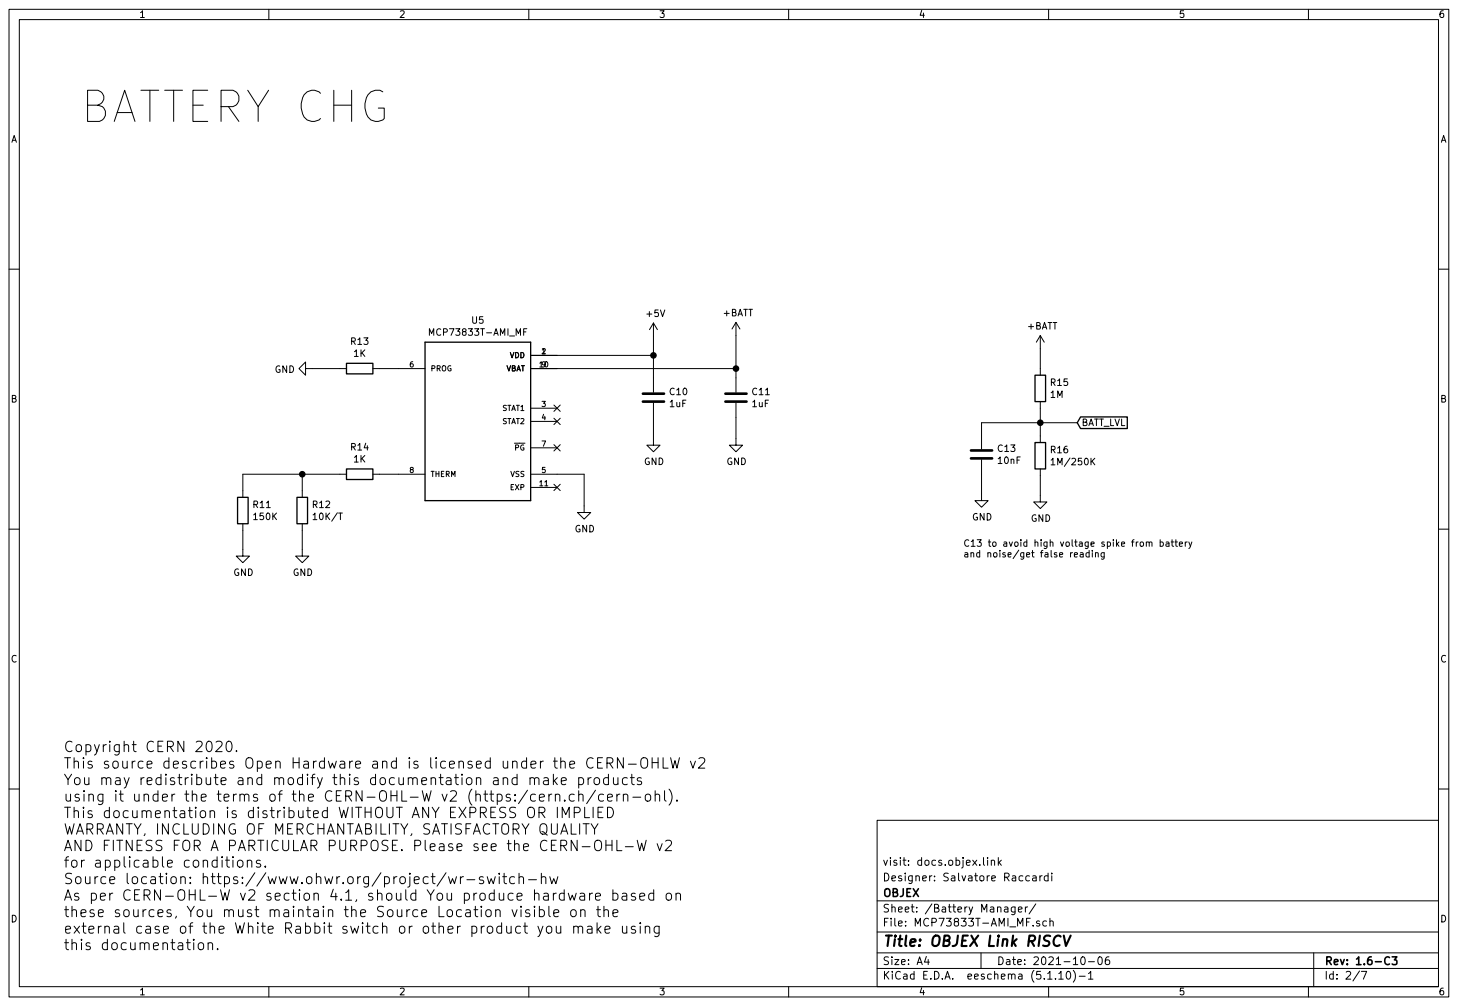
[picture p112: page 2]

C13 to avoid high voltage spike from battery
and noise/get false reading

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

visit: docs.objex.link
Sheet: /Battery Manager/ OBJEX Designer: Salvatore Raccardi

File: MCP73833T-AMI_MF.sch
Id: 2/7 Title: OBJEX Link RISCV


1M GND A1 | VBUS | B8 SHIELD S1

A4 CC1 A5 D+ A6 D-A7 SBU1 A8 CC2 B5 D+ B6 D-B7 SBU2

visit: docs.objex.link R17

File: USB-C_Type2.0.sch Sheet: /USB-C/ OBJEX Designer: Salvatore Raccardi

Id: 3/7 Title: OBJEX Link RISCV

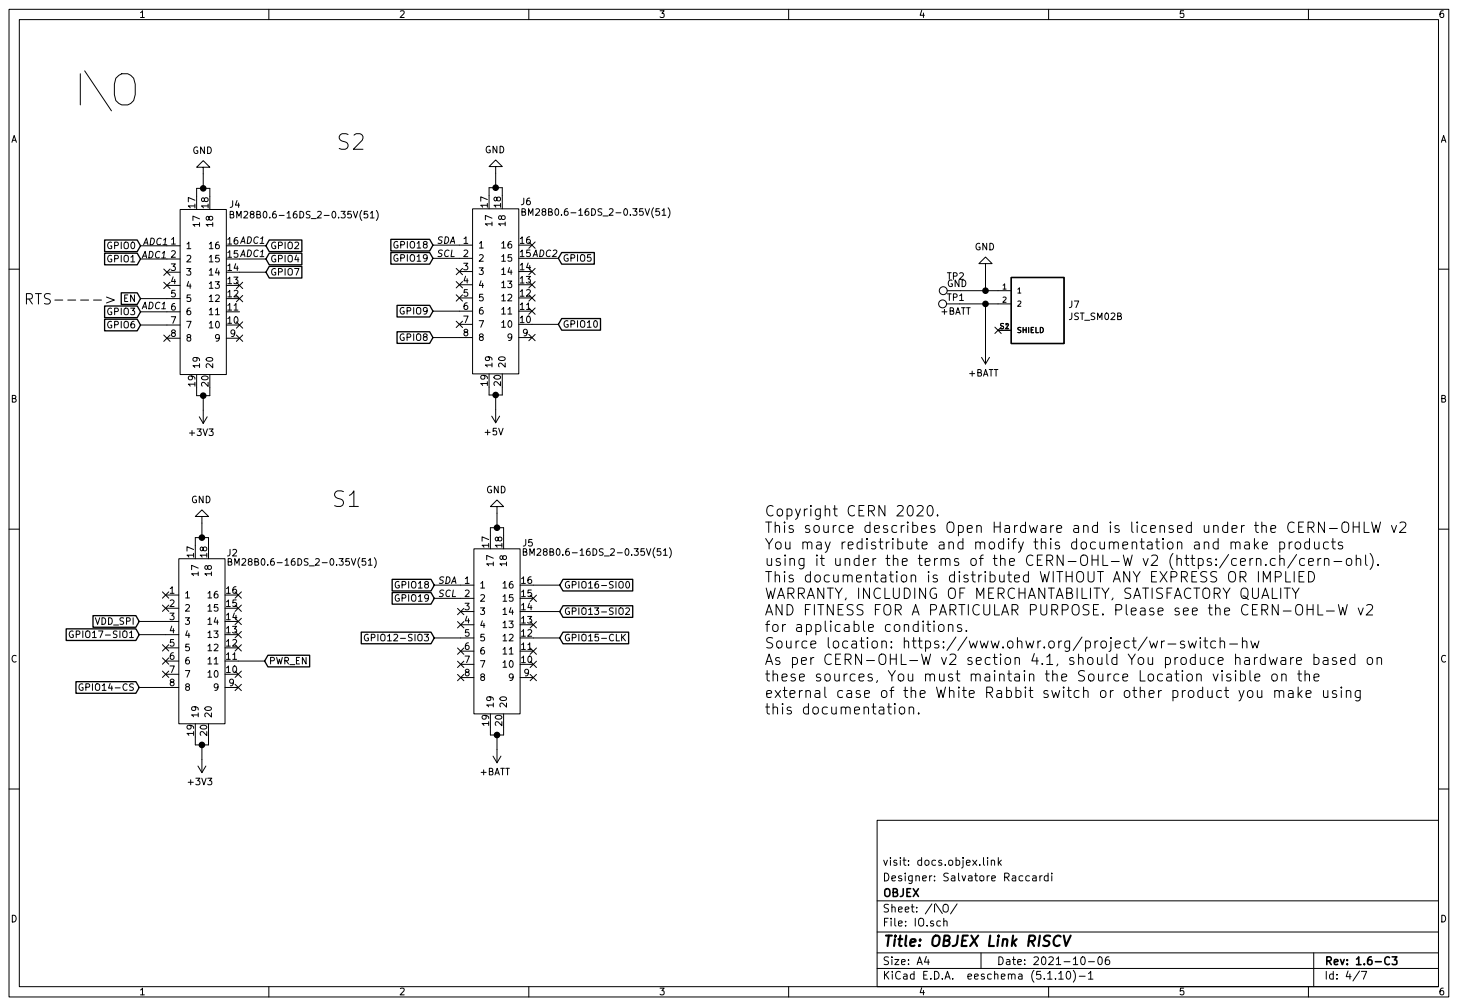
[picture p113: page 4]
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

visit: docs.objex.link
File: IO.sch Sheet: /I\O/ OBJEX Designer: Salvatore Raccardi

Id: 4/7 Title: OBJEX Link RISCV

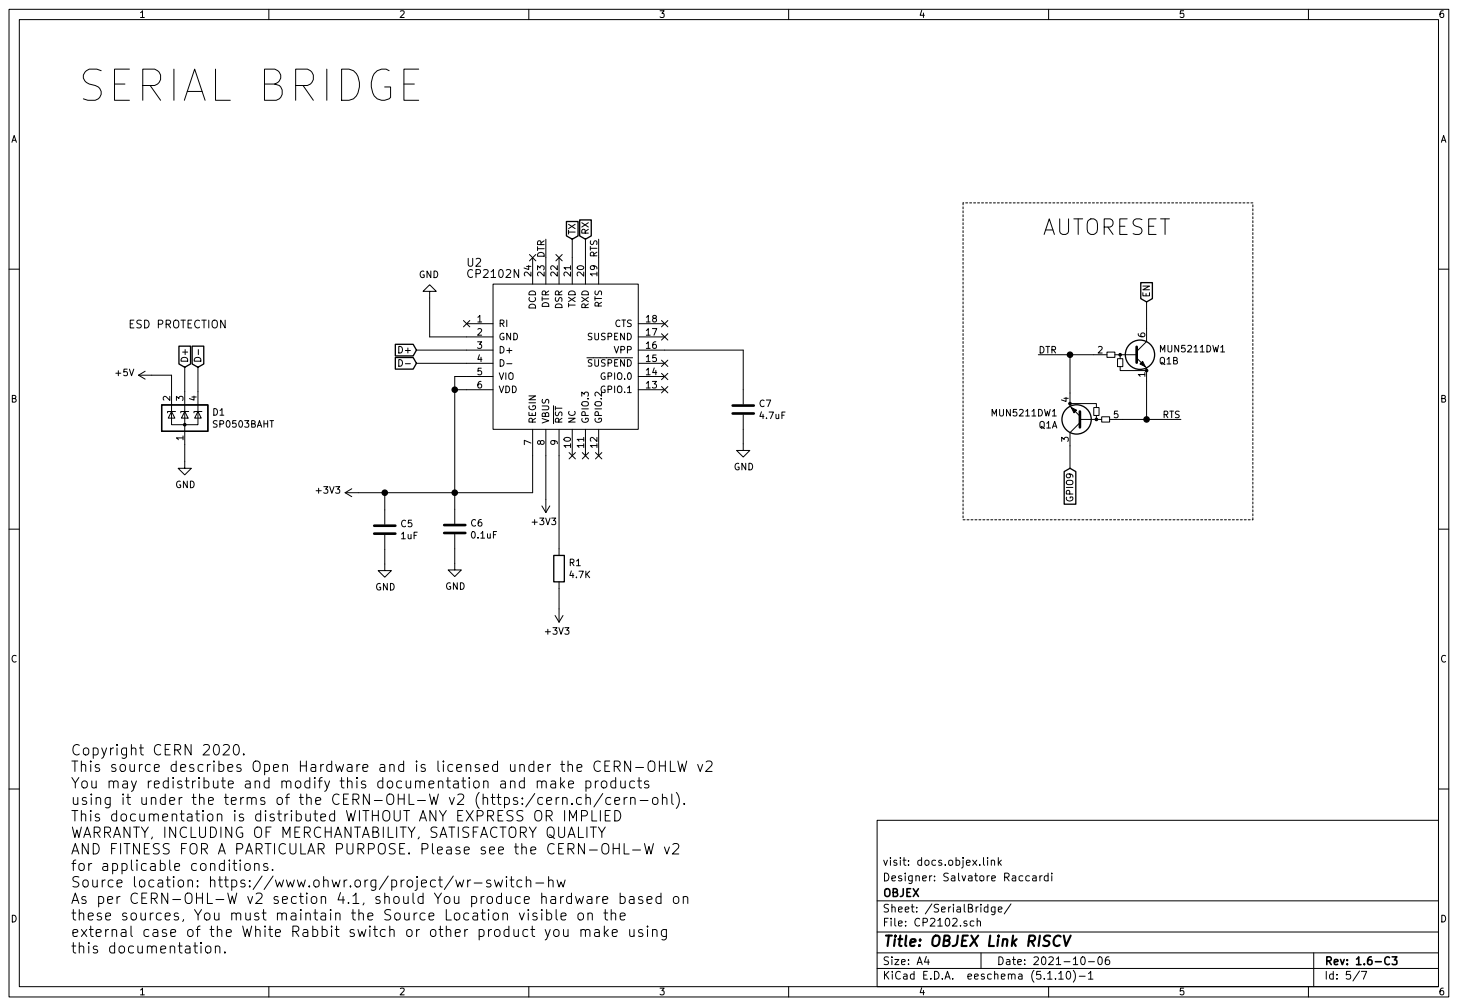
[picture p114: page 5]

9 NC 10 RXD 20 GPIO.3 11 TXD 21 GPIO.2 12 DSR 22 GPIO.1 13 DTR 23 GPIO.0 14 DCD 24 SUSPEND 15 VPP 16 SUSPEND 17 CTS 18 RTS 19U2CP2102N

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

visit: docs.objex.link
File: CP2102.sch Sheet: /SerialBridge/ OBJEX Designer: Salvatore Raccardi

Id: 5/7 Title: OBJEX Link RISCV

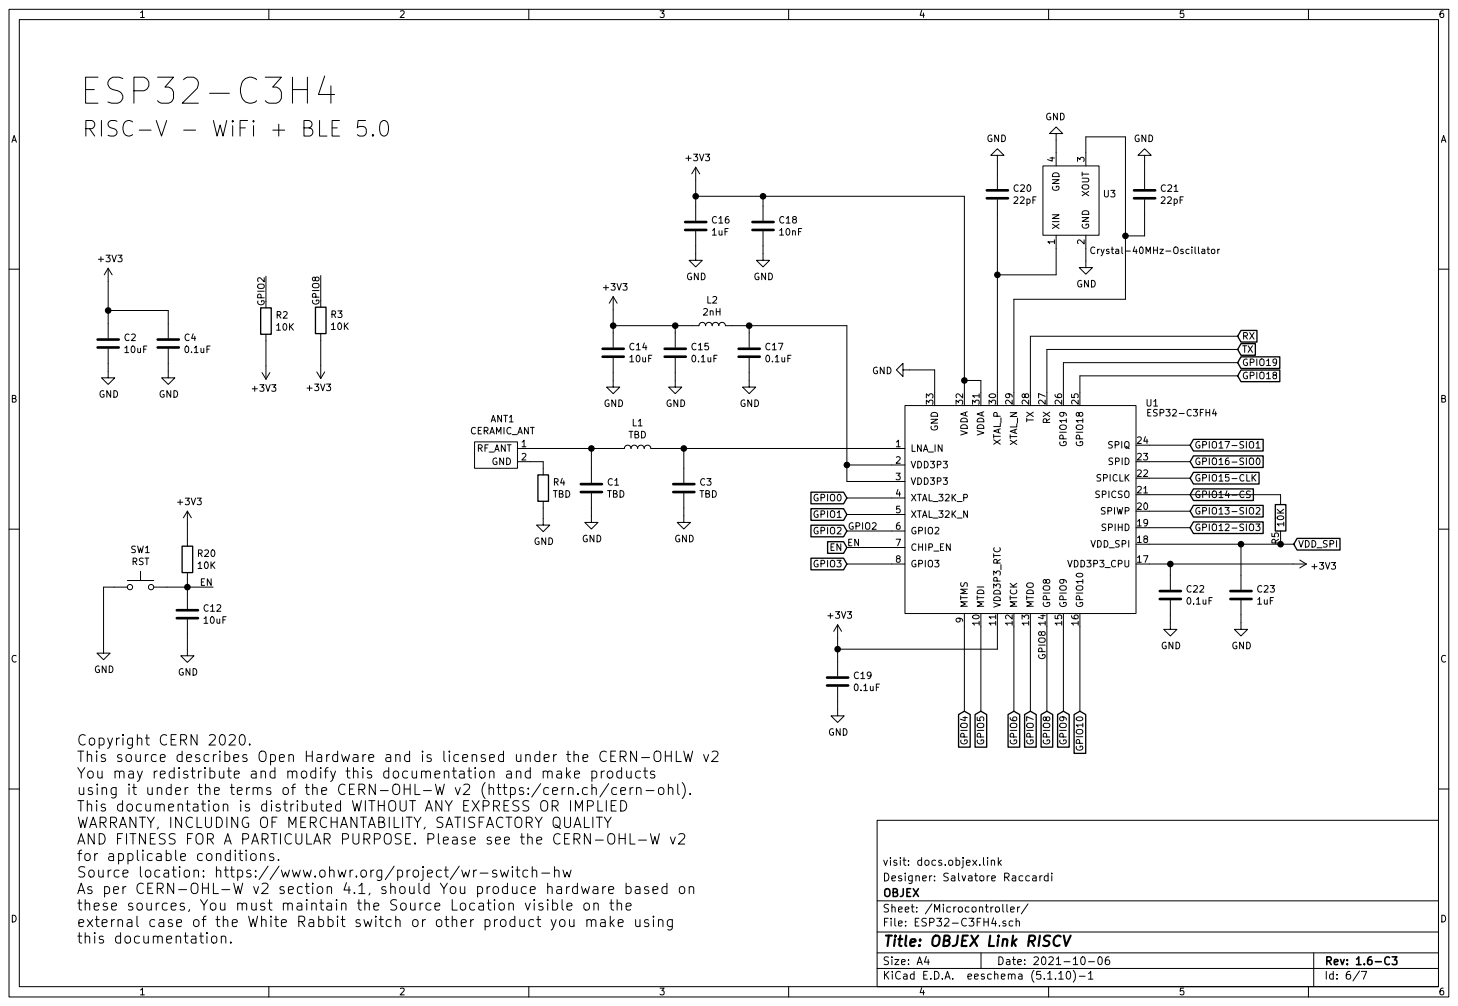
[picture p115: page 6]

visit: docs.objex.link GND
L1 TBD

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

File: ESP32-C3FH4.sch Sheet: /Microcontroller/ OBJEX Designer: Salvatore Raccardi

Id: 6/7 Title: OBJEX Link RISCV

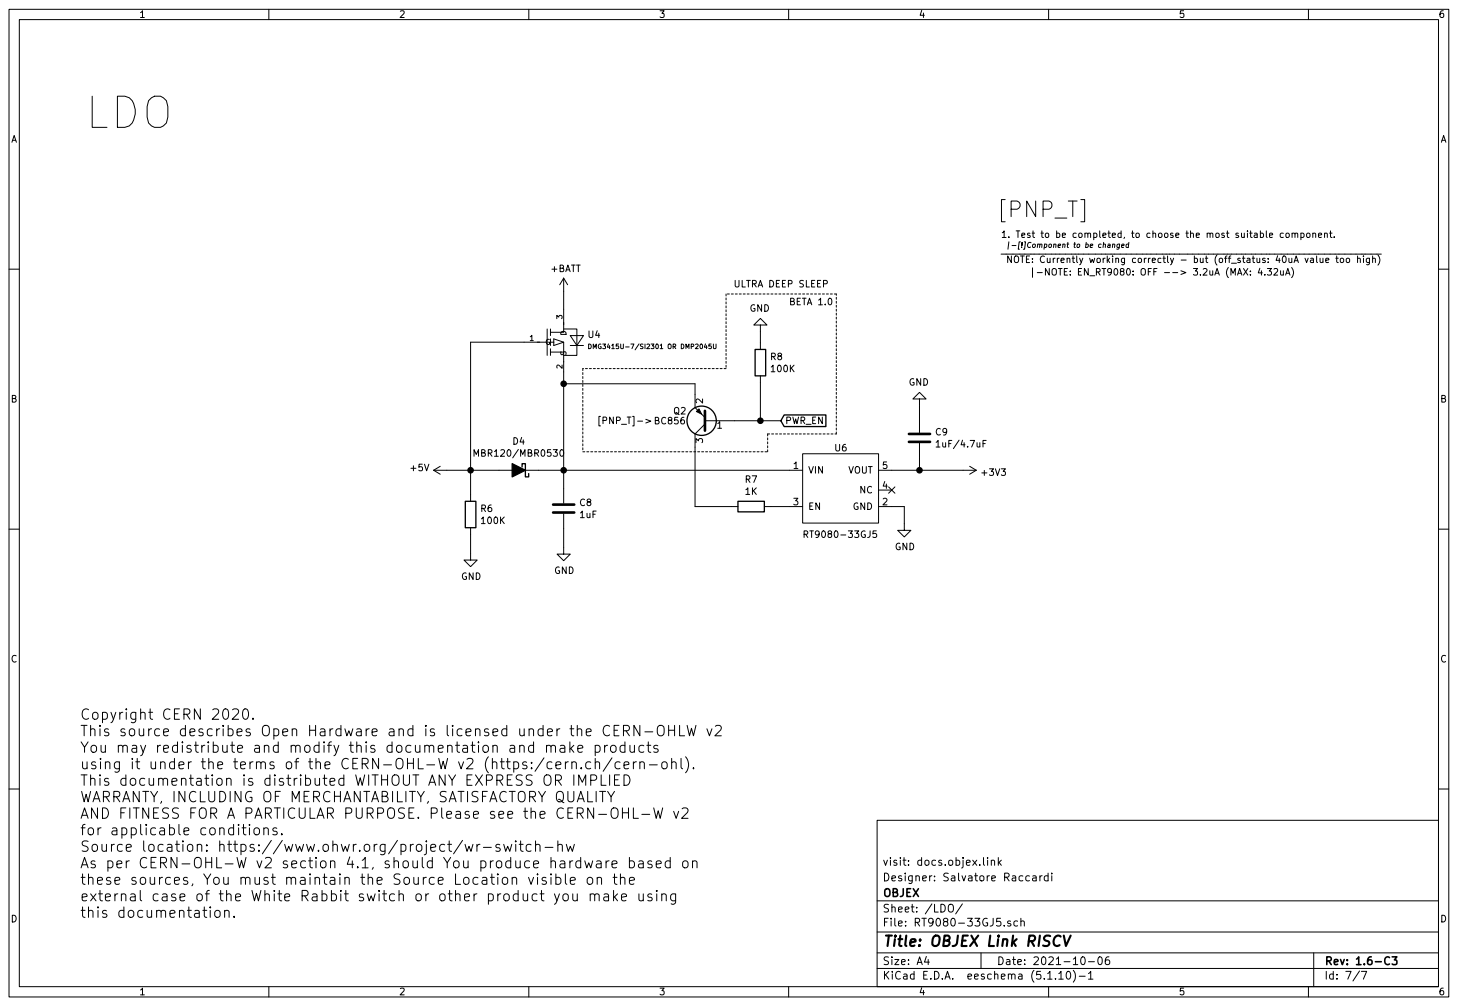
[picture p116: page 7]

-NOTE: EN_RT9080: OFF --> 3.2uA (MAX: 4.32uA) BETA 1.0 ULTRA DEEP SLEEP LDO

1. Test to be completed, to choose the most suitable component.
-[!]Component to be changed
NOTE: Currently working correctly - but (off_status: 40uA value too high)

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

visit: docs.objex.link
File: RT9080-33GJ5.sch Sheet: /LDO/ OBJEX Designer: Salvatore Raccardi

Id: 7/7 Title: OBJEX Link RISCV
